ChanchalSakardeQH/WATERTANK-LEVEL-INDICATOR-with-Dashboard/water_level_indicator/dashboard_html.h

/*
  Water Tanks Monitor System - dashboard web page (HTML, CSS, JavaScript), served from flash
  woodyouloveit.com
  Copyright (C) 2026 Chanchal Sakarde. All Rights Reserved, except as granted by the license below.

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
  SPDX-License-Identifier: GPL-3.0-or-later
*/
// Dashboard web page, served from flash. Works offline (no external files).
#pragma once
#include <Arduino.h>

const char DASHBOARD_HTML[] PROGMEM = R"rawliteral(<!DOCTYPE html>
<html lang="en">
<!--
  Water Tanks Monitor System dashboard - woodyouloveit.com
  Copyright (C) 2026 Chanchal Sakarde. All Rights Reserved, except as granted by the GNU GPL v3 (or later).
  Source: https://github.com/ChanchalSakardeQH/WATERTANK-LEVEL-INDICATOR-with-Dashboard
-->
<head>
<meta charset="utf-8">
<meta name="viewport" content="width=device-width, initial-scale=1, viewport-fit=cover">
<meta name="theme-color" content="#0f766e">
<title>Water Tanks Monitor System | woodyouloveit.com</title>
<meta name="author" content="Chanchal Sakarde, woodyouloveit.com">
<link rel="icon" href="data:image/svg+xml,%3Csvg xmlns='http://www.w3.org/2000/svg' viewBox='0 0 32 32'%3E%3Cpath fill='%23e7004e' d='M16 29 3.5 16.5A7.5 7.5 0 0 1 16 6.2 7.5 7.5 0 0 1 28.5 16.5Z'/%3E%3C/svg%3E">
<style>
:root{--bg:#f1f5f9;--card:#fff;--text:#0f172a;--muted:#64748b;--line:#e2e8f0;--accent:#0f766e;--accent2:#14b8a6;
--danger:#dc2626;--warn:#d97706;--ok:#16a34a;--input:#f8fafc;--shadow:0 1px 3px rgba(15,23,42,.08),0 4px 16px rgba(15,23,42,.05)}
@media (prefers-color-scheme:dark){:root{--bg:#0b1220;--card:#131c2e;--text:#e2e8f0;--muted:#94a3b8;--line:#243047;
--input:#0f1726;--shadow:0 1px 3px rgba(0,0,0,.4)}}
*{box-sizing:border-box}
html,body{margin:0;background:var(--bg);color:var(--text);font-family:-apple-system,BlinkMacSystemFont,"Segoe UI",Roboto,Helvetica,Arial,sans-serif;-webkit-text-size-adjust:100%}
body{padding:env(safe-area-inset-top) env(safe-area-inset-right) env(safe-area-inset-bottom) env(safe-area-inset-left)}
/* brand */
.brandbar{display:flex;align-items:center;justify-content:space-between;gap:12px;background:#fff;padding:10px 20px;border-bottom:1px solid #e2e8f0}
.brandbar img{height:30px;width:auto;display:block}
.brandbar .site{color:#0f172a;font-weight:700;font-size:13px;text-decoration:none;white-space:nowrap}
.brandbar .site:hover{color:#e7004e}
@media (max-width:380px){.brandbar img{height:24px}.brandbar .site{font-size:12px}}
footer{line-height:1.8}footer a{color:inherit;font-weight:600}
.copy{font-weight:600;color:var(--text)}
.pdfrow{display:flex;flex-wrap:wrap;align-items:center;gap:10px 16px;margin-top:14px}
.pdfrow .btn{width:auto;padding:12px 20px}.pdfrow .help{margin:0;flex:1;min-width:200px}
header{display:flex;align-items:center;justify-content:space-between;gap:12px;padding:16px 20px;background:var(--accent);color:#fff}
header h1{font-size:18px;margin:0;font-weight:600;line-height:1.2}
header small{display:block;opacity:.8;font-weight:400;font-size:12px}
.chip{display:inline-flex;align-items:center;gap:6px;padding:5px 12px;border-radius:999px;font-size:13px;font-weight:600;background:rgba(255,255,255,.18);white-space:nowrap}
.chip i{width:8px;height:8px;border-radius:50%;background:#a7f3d0}
.chip.bad i{background:#fca5a5}.chip.warn i{background:#fcd34d}
main{max-width:1100px;margin:0 auto;padding:16px;display:grid;gap:16px;grid-template-columns:1fr}
@media (min-width:860px){main{padding:24px}#tabOverview{grid-template-columns:380px 1fr;grid-template-areas:'ban ban' 'level glance';align-items:start}
#tabAnalytics{grid-template-columns:1fr 1fr;grid-template-areas:'akpi akpi' 'achart achart' 'amotor ause' 'ahour anight' 'aset aset';align-items:start}
#aKpi{grid-area:akpi}#aChart{grid-area:achart}#aMotor{grid-area:amotor}#aUse{grid-area:ause}#aHour{grid-area:ahour}#aNight{grid-area:anight}#aSet{grid-area:aset}
#banners{grid-area:ban}
#tabOverview:has(#banners[hidden]){grid-template-areas:'level glance'}#cLevel{grid-area:level}#cGlance{grid-area:glance}
#tabSetup{grid-template-columns:1fr 1fr;grid-template-areas:'prof cal' 'site cal' 'site disp' 'power disp' 'rate dev' 'admin ota' 'wifi wifi';align-items:start}
#cProfile{grid-area:prof}#cPower{grid-area:power}#cAdmin{grid-area:admin}#cRate{grid-area:rate}#cOta{grid-area:ota}#cCal{grid-area:cal}#cSite{grid-area:site}#cDisp{grid-area:disp}#cWifi{grid-area:wifi}#cDev{grid-area:dev}}
.card{background:var(--card);border-radius:14px;box-shadow:var(--shadow);padding:18px}
.card h2{font-size:15px;margin:0 0 14px;color:var(--muted);font-weight:600;letter-spacing:.02em}
.hero{display:flex;gap:20px;align-items:stretch}
.tank{position:relative;width:110px;min-width:110px;height:230px;border:3px solid var(--line);border-top:none;border-radius:0 0 18px 18px;overflow:hidden;background:var(--input)}
.water{position:absolute;left:0;right:0;bottom:0;height:0;transition:height .8s ease,background-color .8s ease}
.water:before{content:"";position:absolute;left:0;right:0;top:-6px;height:12px;background:inherit;border-radius:50%;opacity:.7}
.leds{display:flex;flex-direction:column-reverse;gap:3px;height:230px;padding:2px 0}
.led{width:12px;flex:1 1 0;min-height:1px;max-height:6px;margin:auto 0;border-radius:2px;background:var(--line);transition:background-color .5s}
.big{font-size:56px;font-weight:700;line-height:1;margin:6px 0 4px}
.big small{font-size:22px;color:var(--muted);font-weight:600}
.kv{display:grid;grid-template-columns:auto 1fr;gap:6px 14px;font-size:14px;margin-top:14px}
.kv span{color:var(--muted)}.kv b{font-weight:600;text-align:right}
.alert{margin-top:12px;padding:10px 12px;border-radius:10px;font-size:13px;font-weight:600;display:none}
.alert.show{display:block}.alert.ok{background:rgba(22,163,74,.12);color:var(--ok)}.alert.info{background:rgba(15,118,110,.12);color:var(--accent)}
.alert a{color:inherit}.alert.bad{background:rgba(220,38,38,.12);color:var(--danger)}.alert.warn{background:rgba(217,119,6,.12);color:var(--warn)}
.live{display:flex;align-items:baseline;justify-content:space-between;padding:12px 14px;border-radius:10px;background:var(--input);margin-bottom:14px}
.live b{font-size:26px}
.row2{display:grid;grid-template-columns:1fr 1fr;gap:12px}
.row3{display:grid;grid-template-columns:1fr 1fr 1fr;gap:10px}.row3[hidden],.row2[hidden]{display:none}
.sel{width:100%;padding:11px 10px;font-size:16px;border:1px solid var(--line);border-radius:10px;background:var(--input);color:var(--text)}
h3.sub{font-size:14px;margin:20px 0 6px;color:var(--text)}
.slide{display:flex;align-items:center;gap:14px;margin:10px 0 6px}.slide input{flex:1;height:32px}.slide b{min-width:96px;text-align:right;font-size:18px}
.calprev{font-size:13px;line-height:1.5;padding:10px 12px;border-radius:10px;background:var(--input);margin:6px 0 10px}
.calprev.bad{background:rgba(220,38,38,.12);color:var(--danger)}.calprev.warn{background:rgba(217,119,6,.12);color:var(--warn)}
.ro{padding:11px 12px;border:1px dashed var(--line);border-radius:10px;font-size:16px}
.help a,.card p a{color:var(--accent);font-weight:600}
.hright{display:flex;align-items:center;gap:8px}
.adminBtn{border:1px solid rgba(255,255,255,.5);background:transparent;color:#fff;border-radius:999px;padding:5px 12px;font-size:13px;font-weight:600;cursor:pointer}
.adminBtn:hover{background:rgba(255,255,255,.15)}
.h2row{display:flex;align-items:center;justify-content:space-between;gap:8px}
.mini{font-size:12px;padding:4px 6px;border:1px solid var(--line);border-radius:8px;background:var(--input);color:var(--text)}
.viewer .adminOnlyNote{display:block}.adminOnlyNote{display:none}
.modal h2{margin-top:0}
.otaBar{height:10px;border-radius:999px;background:var(--input);border:1px solid var(--line);overflow:hidden;margin-top:12px}
.otaBar i{display:block;height:100%;width:0;background:var(--accent);transition:width .2s}
.litres{font-size:15px;color:var(--muted);margin:-2px 0 8px;font-weight:600}
.gstats{display:grid;grid-template-columns:repeat(3,1fr);gap:8px;margin-bottom:14px}.gstats .stat b{font-size:20px}
.seg[id=segUsage]{margin-bottom:0}
label{display:block;font-size:13px;color:var(--muted);margin-bottom:6px}
input[type=number],input[type=text],input[type=password]{width:100%;padding:11px 12px;font-size:16px;border:1px solid var(--line);border-radius:10px;background:var(--input);color:var(--text)}
input[type=range]{width:100%;accent-color:var(--accent)}
.field{margin-bottom:14px}
.btn{appearance:none;border:none;border-radius:10px;padding:12px 14px;min-height:44px;font-size:15px;font-weight:600;cursor:pointer;background:var(--accent);color:#fff;width:100%}
.btn:active{transform:scale(.98)}.btn:disabled{opacity:.5;cursor:not-allowed}
.btn.sec{background:var(--input);color:var(--text);border:1px solid var(--line)}
.btn.danger{background:transparent;color:var(--danger);border:1px solid var(--danger)}
.btns{display:grid;grid-template-columns:1fr 1fr;gap:10px;margin-bottom:12px}
.toggle{display:flex;align-items:center;justify-content:space-between;gap:12px;padding:10px 0;border-top:1px solid var(--line);font-size:14px}
.toggle:first-of-type{border-top:none}
.sw{position:relative;width:48px;height:28px;flex:none}.sw input{opacity:0;width:0;height:0}
.sw i{position:absolute;inset:0;border-radius:999px;background:var(--line);transition:.2s;cursor:pointer}
.sw i:after{content:"";position:absolute;left:3px;top:3px;width:22px;height:22px;border-radius:50%;background:#fff;transition:.2s;box-shadow:0 1px 2px rgba(0,0,0,.3)}
.sw input:checked+i{background:var(--accent)}.sw input:checked+i:after{transform:translateX(20px)}
.help{font-size:12px;color:var(--muted);margin:6px 0 0;line-height:1.5}
.toast{position:fixed;left:50%;bottom:calc(20px + env(safe-area-inset-bottom));transform:translateX(-50%) translateY(120px);background:#0f172a;color:#fff;padding:12px 18px;border-radius:12px;font-size:14px;transition:transform .25s,opacity .25s;z-index:9;opacity:0;visibility:hidden;max-width:90vw;text-align:center}
.toast.show{transform:translateX(-50%) translateY(0);opacity:1;visibility:visible}.toast.err{background:var(--danger)}
.rssi{display:inline-flex;gap:2px;align-items:flex-end;height:14px;vertical-align:middle;margin-left:6px}
.rssi i{width:4px;background:var(--line);border-radius:1px}.rssi i.on{background:var(--ok)}
.modal{position:fixed;inset:0;background:rgba(15,23,42,.55);display:none;align-items:center;justify-content:center;padding:20px;z-index:10}
.modal.show{display:flex}.modal .card{max-width:380px;width:100%}.modal p{margin:0 0 18px;line-height:1.5;font-size:15px}
@media (max-width:380px){.tank{width:84px;min-width:84px}.big{font-size:44px}.hero{gap:14px}}
.wgrid{display:grid;gap:18px}@media (min-width:860px){.wgrid{grid-template-columns:1fr 1fr;gap:32px}}
.scanhead{display:flex;align-items:center;justify-content:space-between;margin-bottom:8px}.scanhead label{margin:0}
.btn.small{width:auto;min-height:36px;padding:8px 16px;font-size:14px}
.netlist{border:1px solid var(--line);border-radius:10px;max-height:230px;overflow-y:auto;margin-bottom:14px;background:var(--input)}
.netlist .help{padding:12px;margin:0}
.net{display:flex;align-items:center;justify-content:space-between;width:100%;gap:10px;padding:12px 14px;border:none;border-top:1px solid var(--line);background:transparent;color:var(--text);font-size:15px;text-align:left;cursor:pointer;min-height:44px}
.net:first-child{border-top:none}.net:hover,.net.sel{background:rgba(20,184,166,.12)}
.net span{overflow:hidden;text-overflow:ellipsis;white-space:nowrap}.net small{color:var(--muted);flex:none;font-size:12px}
.pw{position:relative}.pw input{padding-right:70px}
.eye{position:absolute;right:6px;top:50%;transform:translateY(-50%);border:none;background:transparent;color:var(--accent);font-weight:600;font-size:13px;padding:8px;cursor:pointer}
.banner{background:var(--accent);color:#fff;border-radius:14px;padding:14px 18px;font-size:14px;line-height:1.5;display:none}
.banner.show{display:block}.banner a{color:#fff;font-weight:700}
.stats{display:flex;flex-wrap:wrap;gap:8px;margin-bottom:14px}
.stat{background:var(--input);border:1px solid var(--line);border-radius:10px;padding:8px 12px;font-size:13px;color:var(--muted)}
.stat b{display:block;font-size:18px;color:var(--text)}.stat.bad b{color:var(--danger)}.stat.warn b{color:var(--warn)}
.logbar{display:flex;flex-wrap:wrap;align-items:center;gap:10px;margin-bottom:10px}
.logbar select{padding:9px 10px;font-size:14px;border:1px solid var(--line);border-radius:10px;background:var(--input);color:var(--text)}
.chk{display:flex;align-items:center;gap:6px;font-size:14px;color:var(--text);margin:0}
.logbtns{display:flex;gap:8px;margin-left:auto}
.logbox{max-height:440px;overflow:auto;border:1px solid var(--line);border-radius:10px;background:var(--input);font:12.5px/1.45 ui-monospace,SFMono-Regular,Menlo,Consolas,monospace}
.logbox .help{padding:12px;margin:0;font-family:inherit}
.lr{display:grid;grid-template-columns:150px 56px 1fr;gap:10px;padding:7px 12px;border-top:1px solid var(--line)}
.lr:first-child{border-top:none}.lr time{color:var(--muted);white-space:nowrap}
.lr .tag{color:var(--muted);text-transform:uppercase;font-size:11px;padding-top:1px}
.lr.W .msg{color:var(--warn)}.lr.E .msg{color:var(--danger);font-weight:600}
.lr.boot{background:rgba(15,118,110,.10)}.lr.boot .msg{font-weight:600}
@media (max-width:600px){.lr{grid-template-columns:auto 1fr;gap:2px 10px}.lr .msg{grid-column:1/-1}.logbtns{margin-left:0}}
.tabs{display:flex;gap:4px;background:var(--accent);padding:0 12px;overflow-x:auto}
.tabs button{appearance:none;border:none;background:transparent;color:rgba(255,255,255,.75);font-size:15px;font-weight:600;padding:10px 14px 12px;cursor:pointer;border-bottom:3px solid transparent;white-space:nowrap}
.tabs button.on{color:#fff;border-bottom-color:#fff}
.tab[hidden]{display:none!important}#banners[hidden]{display:none!important}
.kpis{display:grid;grid-template-columns:repeat(auto-fill,minmax(150px,1fr));gap:10px}
.kpi{background:var(--input);border:1px solid var(--line);border-radius:12px;padding:12px}
.kpi span{display:block;font-size:12px;color:var(--muted);font-weight:600;letter-spacing:.02em}
.kpi b{display:block;font-size:20px;margin:4px 0 2px}.kpi small{font-size:12px;color:var(--muted)}
.kpi.bad b{color:var(--danger)}.kpi.warn b{color:var(--warn)}.kpi.ok b{color:var(--ok)}.kpi.live b{color:var(--accent)}
.chart{width:100%;min-height:60px;position:relative}
.chart svg{display:block;width:100%;height:auto;overflow:visible}
.chart .grid{stroke:var(--line);stroke-width:1}.chart .axis{fill:var(--muted);font-size:11px}
.chart .tip{position:absolute;top:0;pointer-events:none;background:var(--text);color:var(--card);font-size:12px;padding:4px 8px;border-radius:6px;white-space:nowrap;display:none;transform:translateX(-50%)}
.seg{display:inline-flex;border:1px solid var(--line);border-radius:10px;overflow:hidden;margin-bottom:10px}
.seg button{border:none;background:var(--input);color:var(--text);padding:8px 14px;font-size:14px;cursor:pointer}
.seg button.on{background:var(--accent);color:#fff}
.legend{display:flex;flex-wrap:wrap;gap:14px;font-size:12px;color:var(--muted);margin-top:6px}
.legend i{display:inline-block;width:12px;height:12px;border-radius:3px;vertical-align:-2px;margin-right:5px}
table.nt{width:100%;border-collapse:collapse;font-size:14px}
.nt th{text-align:left;color:var(--muted);font-weight:600;font-size:12px;padding:6px 4px;border-bottom:1px solid var(--line)}
.nt td{padding:8px 4px;border-bottom:1px solid var(--line)}.nt td:last-child{text-align:right}
.pill{display:inline-block;padding:2px 10px;border-radius:999px;font-size:12px;font-weight:700}
.pill.ok{background:rgba(22,163,74,.14);color:var(--ok)}.pill.warn{background:rgba(217,119,6,.14);color:var(--warn)}
.pill.bad{background:rgba(220,38,38,.14);color:var(--danger)}.pill.na{background:var(--input);color:var(--muted)}
.fl{font-size:13px;margin-top:12px;border-top:1px solid var(--line)}.fl div{padding:7px 0;border-bottom:1px solid var(--line);display:flex;justify-content:space-between;gap:10px}
.fl div span:last-child{color:var(--muted);text-align:right}
select.inp{width:100%;padding:11px 12px;font-size:16px;border:1px solid var(--line);border-radius:10px;background:var(--input);color:var(--text)}
footer{text-align:center;color:var(--muted);font-size:12px;padding:8px 0 24px}
</style>
</head>
<body>
<div class="brandbar">
  <a href="https://woodyouloveit.com" target="_blank" rel="noopener"><img id="brandLogo" alt="woodyouloveit.com" src="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"></a>
  <a class="site" href="https://woodyouloveit.com" target="_blank" rel="noopener">woodyouloveit.com</a>
</div>
<header>
  <h1><span id="hTitle">Water Tanks Monitor System</span><small id="hSub">woodyouloveit.com</small></h1>
  <div class="hright"><div class="chip" id="chip"><i></i><span id="chipText">Connecting…</span></div>
    <button class="adminBtn" id="btnAdmin" onclick="adminClick()">Admin</button></div>
</header>
<nav class="tabs" id="tabs">
  <button data-tab="overview" class="on">Overview</button>
  <button data-tab="analytics">Analytics</button>
  <button data-tab="setup">Setup</button>
  <button data-tab="log">Log</button>
</nav>

<main id="tabOverview" class="tab">
  <div id="banners" style="display:grid;gap:12px">
  <div class="banner" id="siteBanner">Name this tank: add the society or organisation, building and tank in <a href="#cSite">Setup → Site details</a>. The names appear on the dashboard and in reports.</div>
  <div class="banner" id="setupBanner">Not connected to your home Wi-Fi yet. <a href="#cWifi">Set up Wi-Fi</a> in Setup to use the dashboard from your home network.</div>
  </div>

  <section class="card" id="cLevel">
    <h2 class="h2row"><span>WATER LEVEL</span>
      <select id="unitSel" class="mini" title="Units on this device (browser)"><option value="">Units: default</option>
        <option value="0">cm</option><option value="1">mm</option><option value="2">inch</option></select></h2>
    <div class="hero">
      <div class="tank"><div class="water" id="water"></div></div>
      <div class="leds" id="leds" title="LED strip preview"></div>
      <div style="flex:1;min-width:0">
        <div class="big"><span id="pct">--</span><small>%</small></div>
        <div class="litres" id="litres"></div>
        <div class="kv">
          <span>Distance</span><b id="dist">-- cm</b>
          <span>Empty at</span><b id="kvEmpty">-- cm</b>
          <span>Full at</span><b id="kvFull">-- cm</b>
        </div>
      </div>
    </div>
    <div class="alert bad" id="alertFault">Sensor fault: no echo. Check the sensor wiring and that the probe faces the water.</div>
    <div class="alert warn" id="alertLow">Low water level.</div>
    <div class="alert info" id="alertFill"></div>
    <div class="alert bad" id="alertLeak"></div>
  </section>

  <section class="card" id="cGlance">
    <h2>TANK AT A GLANCE</h2>
    <div class="gstats">
      <div class="stat"><b id="gWater">--</b>water now</div>
      <div class="stat"><b id="gFree">--</b>space left</div>
      <div class="stat"><b id="gCap">--</b>capacity</div>
    </div>
    <div class="kv" style="margin-top:0">
      <span>Site</span><b id="gSite">--</b>
      <span>Usage</span><b id="gUsage">--</b>
      <span>Tank</span><b id="gTank">--</b>
      <span>Water depth when full</span><b id="gDepth">--</b>
      <span>Calibrated range</span><b id="gRange">--</b>
      <span>Sensor to full water line</span><b id="gGap">--</b>
      <span id="gResL">1 cm of water</span><b id="gRes">--</b>
    </div>
    <div class="alert warn" id="gWarn"></div>
    <p class="help adminLink" style="margin-top:12px"><a href="#setup">Change tank, usage and calibration in Setup</a></p>
  </section>
</main>

<main id="tabSetup" class="tab" hidden>
  <section class="card" id="cProfile">
    <h2>USAGE &amp; TANK</h2>
    <div class="field"><label>Usage</label>
      <div class="seg" id="segUsage"><button data-v="0" class="on">Domestic</button><button data-v="1">Commercial</button></div></div>
    <div class="row2">
      <div class="field"><label for="inLoc">Tank location</label><select id="inLoc" class="sel">
        <option value="0">Overhead (roof)</option><option value="1">Loft / bathroom</option>
        <option value="2">Underground sump</option><option value="3">Other</option></select></div>
      <div class="field"><label for="inShape">Tank shape</label><select id="inShape" class="sel">
        <option value="0">Rectangular (box, loft)</option><option value="1">Vertical cylinder</option></select></div>
    </div>
    <div class="field"><label for="inPreset">Tank size</label><select id="inPreset" class="sel"></select></div>
    <div class="row3" id="dimRect">
      <div class="field"><label for="inLen">Length (<span class="uL">mm</span>)</label><input type="number" id="inLen" min="0" max="20000" inputmode="numeric"></div>
      <div class="field"><label for="inWid">Width (<span class="uL">mm</span>)</label><input type="number" id="inWid" min="0" max="20000" inputmode="numeric"></div>
      <div class="field"><label for="inHgt">Height (<span class="uL">mm</span>)</label><input type="number" id="inHgt" min="0" max="20000" inputmode="numeric"></div>
    </div>
    <div class="row2" id="dimCyl" hidden>
      <div class="field"><label for="inDia">Diameter (<span class="uL">mm</span>)</label><input type="number" id="inDia" min="0" max="20000" inputmode="numeric"></div>
      <div class="field"><label for="inHgtC">Height (<span class="uL">mm</span>)</label><input type="number" id="inHgtC" min="0" max="20000" inputmode="numeric"></div>
    </div>
    <div class="row2">
      <div class="field"><label for="inDepth">Water depth when full (<span class="uL">mm</span>)</label><input type="number" id="inDepth" min="0" max="20000" inputmode="numeric">
        <p class="help">Tank bottom to the overflow pipe: the highest the water gets.</p></div>
      <div class="field"><label for="inCapP">Capacity (litres)</label><input type="number" id="inCapP" min="0" max="1000000" inputmode="numeric">
        <p class="help" id="capHint"></p></div>
    </div>
    <div class="alert info" id="profTip"></div>
    <div class="btns" style="margin-top:14px">
      <button class="btn" onclick="saveProfile()">Save tank</button>
      <button class="btn sec" onclick="applyRecommended()">Recommended settings</button>
    </div>
    <p class="help" id="recHelp"></p>
  </section>

  <section class="card" id="cCal">
    <h2>CALIBRATION</h2>
    <div class="live"><span>Live sensor reading <small class="help" id="liveMode"></small></span><b id="liveDist">-- cm</b></div>

    <h3 class="sub">1 · How full is the tank right now?</h3>
    <p class="help">Slide to the current water level. With the water depth from <a href="#cProfile">Usage &amp; tank</a>,
      the empty and full points are worked out from the live reading. No need to empty or fill the tank.</p>
    <div class="slide"><input type="range" id="inNow" min="0" max="100" step="1" value="50"><b id="nowVal">50%</b></div>
    <div class="calprev" id="prevSlider"></div>
    <button class="btn" id="btnSlider" onclick="calSlider()">Save calibration from current level</button>

    <h3 class="sub">2 · From measurements</h3>
    <div class="row2">
      <div class="field"><label for="inGap">Sensor face to full water line (<span class="uL">cm</span>)</label><input type="number" id="inGap" step="0.5" min="15" max="400" inputmode="decimal"></div>
      <div class="field"><label>Water depth when full</label><div class="ro" id="depthShow">--</div></div>
    </div>
    <div class="calprev" id="prevMeas"></div>
    <button class="btn sec" id="btnMeas" onclick="calMeasured()">Save calibration from measurements</button>

    <h3 class="sub">3 · Tank is empty or full right now</h3>
    <div class="btns">
      <button class="btn sec" id="btnEmpty" onclick="calNow('empty')">Tank is EMPTY now</button>
      <button class="btn sec" id="btnFull" onclick="calNow('full')">Tank is FULL now</button>
    </div>
    <div class="row2" style="margin-top:4px">
      <div class="field"><label for="inEmpty">Empty distance (<span class="uL">cm</span>)</label><input type="number" id="inEmpty" step="0.5" min="20" max="450" inputmode="decimal"></div>
      <div class="field"><label for="inFull">Full distance (<span class="uL">cm</span>)</label><input type="number" id="inFull" step="0.5" min="15" max="440" inputmode="decimal"></div>
    </div>
    <button class="btn sec" onclick="calManual()">Save distances</button>
    <p class="help">Now: empty at <b id="calNowE">--</b>, full at <b id="calNowF">--</b> from the sensor.
      The sensor can't measure closer than about 20–25 cm, so the full water line must be at least that far below it.</p>
  </section>

  <section class="card" id="cSite">
    <h2>SITE DETAILS</h2>
    <div class="field"><label for="inOrg">Society / organisation</label><input type="text" id="inOrg" maxlength="48" placeholder="e.g. NYATI" autocomplete="organization"></div>
    <div class="row2">
      <div class="field"><label for="inBld">Building</label><input type="text" id="inBld" maxlength="32" placeholder="e.g. Tower A"></div>
      <div class="field"><label for="inTank">Tank</label><input type="text" id="inTank" maxlength="32" placeholder="e.g. Overhead Tank 1"></div>
    </div>
    <div class="kv" style="margin-top:0">
      <span>Hotspot name</span><b id="sAp">--</b>
      <span>Web address</span><b id="sHost">--</b>
    </div>
    <div class="alert info" id="sRestart"></div>
    <div class="btns" style="margin-top:14px">
      <button class="btn" onclick="saveSite()">Save site details</button>
      <button class="btn sec" id="btnSiteRestart" onclick="restartDev()">Restart device</button>
    </div>
    <p class="help">Used on this dashboard, in PDF reports and downloaded logs. The hotspot name and web address are made from the building and tank
      names, so every tank in the society gets its own. They change after a restart.</p>
  </section>

  <section class="card" id="cDisp">
    <h2>DISPLAY &amp; SENSOR SETTINGS</h2>
    <div class="field"><label>Units for everyone (default)</label>
      <div class="seg" id="segUnits" style="margin-bottom:4px"><button data-v="1">mm</button><button data-v="0">cm</button><button data-v="2">inch</button></div>
      <p class="help">Used on the dashboard and in PDF reports. Each viewer can still pick other units in the Water level card.</p></div>
    <div class="field"><label for="inLeds">Number of LEDs on the strip</label><input type="number" id="inLeds" min="1" max="300" step="1" inputmode="numeric">
      <p class="help" id="ampHelp"></p></div>
    <div class="field"><label>LED brightness: <b id="brVal">--</b></label><input type="range" id="inBr" min="5" max="255" step="5"></div>
    <div class="field"><label>Low water alarm below: <b id="lowVal">--</b>%</label><input type="range" id="inLow" min="0" max="50" step="1"></div>
    <div class="toggle"><span>Strip mounted top-down (LED 1 at top)</span><label class="sw"><input type="checkbox" id="inRev"><i></i></label></div>
    <div class="toggle"><span>Whole bar one color (by level)</span><label class="sw"><input type="checkbox" id="inCbl"><i></i></label></div>
    <div class="field" style="margin-top:10px"><label for="inTrig">Sensor trigger pulse (µs)</label><input type="number" id="inTrig" min="10" max="1000" step="10" inputmode="numeric">
      <p class="help">The AJ-SR04M needs 50–500 µs. Default 100.</p></div>
    <div class="btns">
      <button class="btn" onclick="saveSettings()">Save settings</button>
      <button class="btn sec" onclick="resetDefaults()">Defaults</button>
    </div>
  </section>

  <section class="card" id="cPower">
    <h2>POWER &amp; RADIO</h2>
    <div class="toggle" style="border-top:none"><span>Power saving (production mode)<br><span class="help">CPU at 80 MHz (ESP32), LED strip refreshed only when it changes,
      Wi-Fi power saving while the hotspot is off. Recommended for installed devices. How often the sensor is read is set in Update rate.</span></span>
      <label class="sw"><input type="checkbox" id="inEco"><i></i></label></div>
    <div class="field" style="margin-top:10px"><label for="inApMode">Hotspot</label>
      <select id="inApMode" class="sel"><option value="0">Automatic: on when home Wi-Fi is unavailable</option>
        <option value="2">On demand: press BOOT to turn on, off after 10 min idle</option><option value="1">Always on</option></select>
      <p class="help" id="apModeHelp"></p></div>
    <div class="field"><label>Wi-Fi transmit power</label>
      <div class="seg" id="segTx" style="margin-bottom:4px"><button data-v="2">Low</button><button data-v="0">Medium</button><button data-v="1">High</button></div>
      <p class="help">Lower power means less heat and less interference. Use High only if the signal to the router or phone is weak.</p></div>
    <div class="kv" style="margin-top:0">
      <span>Mode now</span><b id="pMode">--</b>
      <span>CPU</span><b id="pCpu">--</b>
      <span>Transmit power</span><b id="pTx">--</b>
      <span>Update rate</span><b id="pRate">--</b>
    </div>
    <div style="margin-top:14px"><button class="btn" onclick="savePower()">Save power settings</button></div>
  </section>

  <section class="card" id="cRate">
    <h2>UPDATE RATE</h2>
    <p class="help" style="margin-top:0">How often the water level is measured, and how often an open dashboard refreshes. Slower means less
      sensor and radio activity, lower power and a cooler board. A tank level changes slowly, so Eco is plenty for daily use.</p>
    <div class="field" style="margin-top:10px"><label for="inRate">Profile</label>
      <select id="inRate" class="sel">
        <option value="0">Eco: sensor every 5 s, dashboard every 10 s (recommended)</option>
        <option value="1">Balanced: sensor every 2 s, dashboard every 5 s</option>
        <option value="2">Responsive: sensor every 0.5 s, dashboard every 2 s</option>
        <option value="3">Custom</option></select></div>
    <div class="row2" id="rateCustom" hidden>
      <div class="field"><label for="inSensS">Sensor reading every (seconds)</label><input type="number" id="inSensS" min="0.2" max="30" step="0.1" inputmode="decimal"></div>
      <div class="field"><label for="inRefS">Dashboard refresh every (seconds)</label><input type="number" id="inRefS" min="2" max="60" step="1" inputmode="numeric"></div>
    </div>
    <div class="kv" style="margin-top:0">
      <span>Sensor readings</span><b id="rPerH">--</b>
      <span>Level follows a change within</span><b id="rReact">--</b>
      <span>"No echo" shown after</span><b id="rFault">--</b>
      <span>Open dashboard refreshes</span><b id="rRefresh">--</b>
    </div>
    <p class="help">Not affected: history (every 2 min), fill detection (every 10 s) and the night leak check.
      While an admin has this Setup tab open, the device reads every 0.5 s so calibration stays live, then returns to this rate.</p>
    <div style="margin-top:12px"><button class="btn" onclick="saveRate()">Save update rate</button></div>
  </section>

  <section class="card" id="cOta">
    <h2>FIRMWARE UPDATE</h2>
    <div class="kv" style="margin-top:0">
      <span>Installed</span><b id="otaCur">--</b>
      <span>Board</span><b id="otaBoard">--</b>
      <span>Space for an update</span><b id="otaMax">--</b>
    </div>
    <p class="help">In Arduino IDE use <b>Sketch → Export Compiled Binary</b>, then pick <b>water_level_indicator.ino.bin</b> from the sketch's
      <b>build</b> folder (not the .bootloader, .partitions or .merged file). Settings, Wi-Fi, calibration, history and logs are kept.</p>
    <input type="file" id="fileOta" accept=".bin,application/octet-stream" hidden onchange="otaPick(this)">
    <div style="margin-top:12px"><button class="btn" id="btnOta" onclick="$('fileOta').click()">Choose firmware file…</button></div>
    <div class="otaBar" id="otaBar" hidden><i id="otaFill"></i></div>
    <p class="help" id="otaMsg"></p>
  </section>

  <section class="card" id="cAdmin">
    <h2>ADMIN &amp; BACKUP</h2>
    <p class="help" style="margin-top:0">Without logging in, people see the Overview and Analytics tabs only. They can't change settings,
      clear history, or restart the device.</p>
    <div class="btns" style="margin-top:12px">
      <button class="btn sec" onclick="openPwModal(false)">Change password</button>
      <button class="btn sec" onclick="adminLogout()">Log out</button>
    </div>
    <h3 class="sub">Settings backup</h3>
    <p class="help">Saves site, tank, calibration, units, alarms, analytics, display and power settings to a file, to restore later or
      on another device, and to attach to reports. Wi-Fi passwords and the admin password are never included.</p>
    <div class="kv" style="margin:8px 0 0"><span>Settings ID now</span><b id="setId">--</b></div>
    <div class="btns" style="margin-top:12px">
      <button class="btn" onclick="exportSettings()">Export settings</button>
      <button class="btn sec" onclick="$('fileImport').click()">Import settings</button>
    </div>
    <input type="file" id="fileImport" accept=".json,application/json" hidden onchange="importSettings(this)">
    <p class="help">The Settings ID also appears in PDF reports, so a report can be matched to the exported settings file.</p>
  </section>

  <section class="card" id="cWifi">
    <h2>WI-FI SETTINGS</h2>
    <div class="wgrid">
      <div>
        <div class="kv" style="margin-top:0">
          <span>Home network</span><b id="wSaved">--</b>
          <span>Status</span><b id="wState">--</b>
          <span>Signal</span><b><span id="rssiTxt">--</span><span class="rssi" id="rssiBars"><i style="height:4px"></i><i style="height:7px"></i><i style="height:10px"></i><i style="height:14px"></i></span></b>
          <span>Home address</span><b id="wIp">--</b>
          <span>Hotspot</span><b id="wAp">--</b>
        </div>
        <div class="alert" id="wMsg"></div>
        <p class="help" style="margin-top:12px">The hotspot <b class="apName">--</b> lets you reach this page at <b>http://192.168.4.1</b> when the device isn't on your home Wi-Fi.
          If it's off, press the <b>BOOT</b> button on the board to turn it on.</p>
        <p class="help">Hotspot mode: <b id="wApMode">--</b>. <a href="#cPower">Change in Power &amp; radio</a>.</p>
      </div>
      <div>
        <div class="scanhead"><label>Available networks</label><button class="btn sec small" id="btnScan" onclick="scan()">Scan</button></div>
        <div class="netlist" id="netList"><p class="help">Press Scan to find networks.</p></div>
        <div class="field"><label for="inSsid">Network name (SSID)</label><input type="text" id="inSsid" maxlength="32" autocomplete="off" autocapitalize="none" autocorrect="off" spellcheck="false"></div>
        <div class="field"><label for="inPass">Password</label><div class="pw"><input type="password" id="inPass" maxlength="63" autocomplete="off" autocapitalize="none" autocorrect="off" spellcheck="false"><button type="button" class="eye" id="btnEye" onclick="togglePw()">Show</button></div></div>
        <div class="btns">
          <button class="btn" onclick="connectWifi()">Connect</button>
          <button class="btn danger" onclick="forgetWifi()">Forget Wi-Fi</button>
        </div>
        <p class="help">Leave the password empty for open networks.</p>
      </div>
    </div>
  </section>

  <section class="card" id="cDev">
    <h2>DEVICE</h2>
    <div class="kv" style="margin-top:0">
      <span>Board</span><b id="board">--</b>
      <span>Firmware</span><b id="fw">--</b>
      <span>Uptime</span><b id="uptime">--</b>
      <span>Last restart</span><b id="reset">--</b>
      <span>Boot count</span><b id="boot">--</b>
      <span>Free memory</span><b id="heap">--</b>
      <span id="vccL">Supply voltage</span><b id="vcc">--</b>
      <span>Log storage</span><b id="logStore">--</b>
    </div>
    <div style="margin-top:16px"><button class="btn sec" onclick="restartDev()">Restart device</button></div>
  </section>
</main>

<main id="tabAnalytics" class="tab" hidden>
  <section class="card" id="aKpi">
    <h2>TANK ANALYTICS</h2>
    <div class="alert info" id="aMsg"></div>
    <div class="kpis" id="kpis"></div>
    <div class="pdfrow">
      <button class="btn" id="btnPdf" onclick="exportPdf()">Download PDF report</button>
      <p class="help">Last 7 days with charts, fills and night checks, branded with the woodyouloveit.com logo.
        On the hotspot's pop-up page, open the dashboard in your normal browser first so the download is allowed.</p>
    </div>
  </section>
  <section class="card" id="aChart">
    <h2>LEVEL HISTORY</h2>
    <div class="seg" id="rangeSeg"><button data-h="24" class="on">24 h</button><button data-h="72">3 days</button><button data-h="168">7 days</button><button data-h="336">14 days</button></div>
    <div class="chart" id="levelChart"></div>
    <div class="legend"><span><i style="background:rgba(22,163,74,.22)"></i>Filling (motor on)</span><span><i style="background:rgba(100,116,139,.16)"></i>Night check window</span></div>
  </section>
  <section class="card" id="aMotor">
    <h2>MOTOR RUN TIME PER DAY</h2>
    <div class="chart" id="motorChart"></div>
    <div class="fl" id="fillList"></div>
  </section>
  <section class="card" id="aUse">
    <h2>WATER USED PER DAY</h2>
    <div class="chart" id="useChart"></div>
    <p class="help">Counted from level drops outside fills. Small changes below the sensor noise are ignored.</p>
  </section>
  <section class="card" id="aHour">
    <h2>USAGE BY HOUR OF DAY</h2>
    <div class="chart" id="hourChart"></div>
    <p class="help" id="hourHelp">Average per day. The busiest hours are highlighted.</p>
  </section>
  <section class="card" id="aNight">
    <h2>NIGHT LEAK CHECK</h2>
    <div id="nightTable"></div>
    <p class="help" id="nightHelp"></p>
  </section>
  <section class="card adminOnly" id="aSet">
    <h2>ANALYTICS SETTINGS</h2>
    <div class="alert info adminOnlyNote" id="aSetNote" style="margin:0 0 14px">View only. <a href="#" onclick="openLogin();return false">Log in as admin</a> to change analytics settings or clear the history.</div>
    <div class="row2">
      <div class="field"><label for="inCap">Tank capacity (litres)</label><input type="number" id="inCap" min="0" max="1000000" step="50" inputmode="numeric" placeholder="e.g. 1000">
        <p class="help">Optional. Shows amounts in litres (assumes straight tank walls). 0 = show %.</p></div>
      <div class="field"><label for="inFillCm">Fill detection: minimum rise (<span class="uL">cm</span>/min)</label><input type="number" id="inFillCm" min="0.1" max="20" step="0.1" inputmode="decimal">
        <p class="help">Lower it if slow fills are missed, raise it if you see false fills. Default 0.5 cm/min.</p></div>
    </div>
    <div class="row2">
      <div class="field"><label for="inNs">Night check from</label><select class="inp" id="inNs"></select></div>
      <div class="field"><label for="inNe">to</label><select class="inp" id="inNe"></select></div>
    </div>
    <div class="field"><label for="inLeak">Possible leak if the level drops more than (<span class="uL">cm</span>) during the night window</label><input type="number" id="inLeak" min="0.2" max="50" step="0.1" inputmode="decimal">
      <p class="help">Pick a quiet time when nobody uses water. Default 01:00–05:00 and 1.5 cm.</p></div>
    <div class="btns">
      <button class="btn" onclick="saveAnalytics()">Save analytics settings</button>
      <button class="btn danger" onclick="clearHistory()">Clear history</button>
    </div>
  </section>
</main>

<main id="tabLog" class="tab" hidden>
  <section class="card" id="cLog">
    <h2>CONNECTIVITY LOG</h2>
    <div class="stats" id="logStats"></div>
    <div class="logbar">
      <select id="logFilter" onchange="renderLog()">
        <option value="all">All events</option><option value="net">Wi-Fi &amp; hotspot</option>
        <option value="warn">Warnings &amp; errors</option><option value="boot">Restarts</option>
      </select>
      <label class="chk"><input type="checkbox" id="logAuto" checked> Auto-refresh</label>
      <div class="logbtns">
        <button class="btn sec small" onclick="loadLog()">Refresh</button>
        <button class="btn sec small" onclick="downloadLog()">Download</button>
        <button class="btn danger small" onclick="clearLog()">Clear</button>
      </div>
    </div>
    <div class="logbox" id="logBox"><p class="help">Loading…</p></div>
    <p class="help">Newest first. Saved in flash, so it survives restarts and power cuts (about 300–400 events).
      Events from before the clock was known show as boot number + time since that start.</p>
  </section>
</main>
<footer>
  <div><span id="fSite">Water Tanks Monitor System</span> · <span id="host"></span></div>
  <div class="copy">© 2026 Chanchal Sakarde. All Rights Reserved. · <a href="https://woodyouloveit.com" target="_blank" rel="noopener">woodyouloveit.com</a></div>
  <div>Open source under the <a href="https://www.gnu.org/licenses/gpl-3.0.html" target="_blank" rel="noopener">GNU GPL v3</a> ·
    <a href="https://github.com/ChanchalSakardeQH/WATERTANK-LEVEL-INDICATOR-with-Dashboard" target="_blank" rel="noopener">Source code</a></div>
</footer>
<div class="toast" id="toast"></div>
<div class="modal" id="loginModal"><div class="card"><h2>ADMIN LOGIN</h2>
  <div class="field"><label for="inPw">Password</label><input type="password" id="inPw" autocomplete="current-password"></div>
  <p class="help" id="loginErr" style="color:var(--danger)"></p>
  <div class="btns" style="margin:0"><button class="btn sec" onclick="closeLogin()">Cancel</button><button class="btn" id="btnLogin" onclick="doLogin()">Log in</button></div>
  <p class="help" style="margin-top:12px">Forgot it? Hold the <b>BOOT</b> button on the board for 10 seconds (the strip flashes red) to reset the password to <b>admin</b>.</p>
</div></div>
<div class="modal" id="pwModal"><div class="card"><h2>CHANGE ADMIN PASSWORD</h2>
  <p class="help" id="pwNote"></p>
  <div class="field"><label for="inPw1">New password</label><input type="password" id="inPw1" autocomplete="new-password"></div>
  <div class="field"><label for="inPw2">Repeat new password</label><input type="password" id="inPw2" autocomplete="new-password"></div>
  <p class="help" id="pwErr" style="color:var(--danger)"></p>
  <div class="btns" style="margin:0"><button class="btn sec" id="btnPwCancel" onclick="closePwModal()">Cancel</button><button class="btn" onclick="savePw()">Save password</button></div>
</div></div>
<div class="modal" id="modal"><div class="card"><p id="modalMsg"></p>
  <div class="btns" style="margin:0"><button class="btn sec" id="modalNo">Cancel</button><button class="btn" id="modalYes">OK</button></div></div></div>

<script>
const $=id=>document.getElementById(id);
const sleep=ms=>new Promise(r=>setTimeout(r,ms));
let N=0,st=null,formLoaded=false,online=false,timeSent=false,logRows=[];
function buildLeds(n){if(n===N)return;N=n;const box=$('leds');box.innerHTML='';
  box.style.gap=(n<=40?3:n<=80?2:n<=120?1:0)+'px';
  for(let i=0;i<n;i++){const d=document.createElement('div');d.className='led';box.appendChild(d);}}
const posT=i=>N>1?i/(N-1):1;

function ledColor(t){t=Math.min(1,Math.max(0,t));let r,g;
  if(t<.5){r=255;g=Math.round(t*510);}else{r=Math.round((1-t)*510);g=255;}return `rgb(${r},${g},0)`;}
function toast(msg,err){const t=$('toast');t.textContent=msg;t.className='toast show'+(err?' err':'');
  clearTimeout(t._h);t._h=setTimeout(()=>t.className='toast'+(err?' err':''),3500);}
function ask(msg){return new Promise(res=>{$('modalMsg').textContent=msg;$('modal').classList.add('show');
  const done=v=>{$('modal').classList.remove('show');res(v);};$('modalYes').onclick=()=>done(true);$('modalNo').onclick=()=>done(false);});}
function fmtUp(s){const d=Math.floor(s/86400),h=Math.floor(s%86400/3600),m=Math.floor(s%3600/60);
  return (d?d+'d ':'')+(d||h?h+'h ':'')+m+'m';}
function bars(rssi){return rssi>-55?4:rssi>-65?3:rssi>-75?2:1;}
function setAlert(el,cls,html){el.className='alert'+(cls?' show '+cls:'');if(cls)el.innerHTML=html;}
function esc(s){const d=document.createElement('div');d.textContent=s;return d.innerHTML;}

function render(){
  const s=st,w=s.wifi,lvl=s.valid?s.level:0;
  $('pct').textContent=s.valid?Math.round(s.level):'--';
  $('dist').textContent=s.valid?fmtL(s.distance):'no echo';
  $('liveDist').textContent=s.valid?fmtL(s.distance):'no echo';
  if($('liveMode'))$('liveMode').textContent=s.rate&&s.rate.live?'· live, every 0.5 s':'';
  $('kvEmpty').textContent=fmtL(s.empty);$('kvFull').textContent=fmtL(s.full);
  const wt=$('water');wt.style.height=(s.valid?lvl:0)+'%';wt.style.backgroundColor=ledColor(lvl/100);
  buildLeds(s.leds);
  const lit=lvl/100*N,leds=$('leds').children;
  for(let i=0;i<N;i++){const on=s.valid&&i<Math.round(lit);
    leds[i].style.backgroundColor=on?ledColor(s.colorByLevel?lvl/100:posT(i)):'';}
  const low=s.valid&&lvl<s.lowAlarm;
  $('alertFault').classList.toggle('show',!s.valid);$('alertLow').classList.toggle('show',low);
  $('chip').className='chip'+(!s.valid?' bad':low?' warn':'');
  $('chipText').textContent=!s.valid?'Sensor fault':low?'Low water':'Online';
  $('btnEmpty').disabled=$('btnFull').disabled=!s.valid;

  // Wi-Fi
  const conn=w.state==='connected';
  $('setupBanner').classList.toggle('show',!w.saved&&w.state!=='connecting'&&!conn);
  renderSite();if(!siteLoaded)fillSite();
  applyUnitLabels();applyRole();
  renderGlance();renderPower();if(!profLoaded)fillProfile();else if(tab==='setup')calPreview();
  if(isAdmin()){$('setId').textContent=settingsId();renderOta();fillRate();}
  $('banners').hidden=!isAdmin()||!document.querySelector('#banners .banner.show');   // setup banners are for admins
  $('wSaved').textContent=w.saved||'Not set';
  $('wState').textContent={connected:'Connected',connecting:'Connecting…',failed:'Not reachable',none:'Not set up'}[w.state];
  $('rssiTxt').textContent=conn?w.rssi+' dBm':'--';
  [...$('rssiBars').children].forEach((b,i)=>b.classList.toggle('on',conn&&i<bars(w.rssi)));
  $('wIp').textContent=conn?w.ip:'--';
  $('wAp').textContent=w.ap?`On · ${w.apClients} device${w.apClients==1?'':'s'}`:'Off';
  const m=$('wMsg');
  if(w.state==='connecting')setAlert(m,'info',esc(w.msg));
  else if(conn&&w.ap&&w.apOffIn>0)setAlert(m,'ok',`Connected to <b>${esc(w.ssid)}</b>. Switch your phone or PC back to your home Wi-Fi and open
    <a href="http://${w.host}.local">http://${w.host}.local</a> or <a href="http://${w.ip}">http://${w.ip}</a>.
    The hotspot turns off in ${w.apOffIn} s.`);
  else if(w.state==='failed')setAlert(m,'bad',esc(w.msg));
  else if(w.state==='none')setAlert(m,'info',esc(w.msg));
  else setAlert(m,'','');

  $('board').textContent=s.board;$('fw').textContent=s.fw;$('uptime').textContent=fmtUp(s.uptime);$('reset').textContent=s.reset;
  $('boot').textContent='#'+s.boot;$('heap').textContent=(s.heap/1024).toFixed(1)+' KB (lowest '+(s.minHeap/1024).toFixed(1)+' KB)';
  $('vcc').textContent=s.vcc?(s.vcc/1000).toFixed(2)+' V':'';$('vcc').style.display=$('vccL').style.display=s.vcc?'':'none';
  $('logStore').textContent=s.logStore==='flash'?'Flash (kept after restart)':'Memory only (lost on restart)';
  $('host').textContent=conn?`${w.host}.local · ${w.ip}`:`hotspot · ${w.apIp}`;
  const fa=$('alertFill');
  if(s.filling)setAlert(fa,'info',`Filling (motor on) · rising ${fmtRate(s.fillRate)}`+(s.fillEta>=0?` · full in about ${dur(s.fillEta)}`:''));
  else setAlert(fa,'','');
  if(!formLoaded)fillForm();
}

// ---- Usage & tank profile ----
// Loft tank sizes (rated litres; outer length x width x height in mm)
const PRESETS=[null,
  {cap:150,l:710,w:710,h:400},{cap:225,l:1035,w:725,h:385},{cap:270,l:1100,w:735,h:425},
  {cap:400,l:1120,w:875,h:420},{cap:500,l:1450,w:915,h:445},{cap:1000,l:1650,w:1080,h:685}];
const USAGE=['Domestic','Commercial'],LOCS=['Overhead (roof)','Loft / bathroom','Underground sump','Other'];
let usageSel=0,profLoaded=false;
const iv=id=>{const v=parseFloat($(id).value);return isFinite(v)?v:0;};
function presetLabel(i){const p=PRESETS[i];return `Loft tank ${p.cap} L · ${p.l} × ${p.w} × ${p.h} mm`;}
function buildPresets(){const sel=$('inPreset'),shape=+$('inShape').value,cur=sel.value;
  sel.innerHTML='<option value="0">Custom size</option>'+(shape===0?PRESETS.slice(1).map((p,i)=>`<option value="${i+1}">${presetLabel(i+1)}</option>`).join(''):'');
  sel.value=[...sel.options].some(o=>o.value===cur)?cur:'0';}
function tankHeight(){return +$('inShape').value?mmIn('inHgtC'):mmIn('inHgt');}
function capEstimate(){const d=mmIn('inDepth');if(!d)return 0;
  return +$('inShape').value?Math.PI*Math.pow(mmIn('inDia')/2,2)*d/1e6*0.95:mmIn('inLen')*mmIn('inWid')*d/1e6*0.85;}
function profileUI(){
  const shape=+$('inShape').value,loc=+$('inLoc').value;
  $('dimRect').hidden=shape!==0;$('dimCyl').hidden=shape!==1;
  $('inPreset').disabled=shape!==0;
  const est=capEstimate();
  $('capHint').textContent=est?`Estimated from the size: about ${Math.round(est)} L. Enter the rated capacity if you know it.`:'Rated capacity from the tank label or catalogue.';
  const tips={1:`Loft tanks are shallow. The sensor cannot measure closer than ${fmtL(20,0)}–${fmtL(25,0)}, so mount it on a stand pipe (at least ${fmtL(25,0)} tall and ${fmtL(7.5,ul()==='in'?1:undefined)} wide) over the manhole, not flat on the lid.`,
    2:'Underground sump: keep the probe away from the inlet pipe and walls. The low water alarm helps protect the pump from running dry.',
    0:`Overhead tank: mount the probe at the centre of the lid or manhole, pointing straight down, at least ${fmtL(25,0)} above the full water line.`};
  setAlert($('profTip'),tips[loc]?'info':'',tips[loc]||'');
  const r=recommended();
  $('recHelp').textContent=`Recommended for ${USAGE[usageSel].toLowerCase()} use, ${LOCS[loc].toLowerCase()}: night leak check ${hh(r.nightStart)}–${hh(r.nightEnd)}, `+
    `low water alarm ${r.lowAlarm}%, leak limit ${fmtL(r.leakCm)}.`;
  $('depthShow').textContent=mmIn('inDepth')?fmtMmL(mmIn('inDepth')):'Set it in Usage & tank';
  calPreview();
}
function recommended(){const loc=+$('inLoc').value,depth=mmIn('inDepth')||spanMm();
  return {nightStart:usageSel?22:1,nightEnd:usageSel?6:5,lowAlarm:loc===2?30:usageSel?25:15,
    leakCm:Math.max(1,Math.round(depth*0.02/5)*0.5)};}
function fillProfile(){if(profLoaded||!st.profile)return;profLoaded=true;const p=st.profile;
  usageSel=p.usage;[...$('segUsage').children].forEach(b=>b.classList.toggle('on',+b.dataset.v===usageSel));
  $('inLoc').value=p.location;$('inShape').value=p.shape;buildPresets();$('inPreset').value=String(p.preset);
  if(!$('inPreset').value)$('inPreset').value='0';
  setMm('inLen',p.len);setMm('inWid',p.wid);setMm('inHgt',p.hgt);setMm('inDia',p.dia);setMm('inHgtC',p.hgt);
  setMm('inDepth',p.depth);$('inCapP').value=st.capacity||'';
  setCm('inGap',st.full);$('inNow').value=Math.round(st.valid?st.level:50);$('nowVal').textContent=$('inNow').value+'%';
  profileUI();}
[...$('segUsage').children].forEach(b=>b.onclick=()=>{usageSel=+b.dataset.v;
  [...$('segUsage').children].forEach(x=>x.classList.toggle('on',x===b));profileUI();});
$('inShape').onchange=()=>{buildPresets();profileUI();};
$('inLoc').onchange=()=>{if(+$('inLoc').value===1&&+$('inShape').value!==0){$('inShape').value='0';buildPresets();}profileUI();};
$('inPreset').onchange=()=>{const p=PRESETS[+$('inPreset').value];
  if(p){setMm('inLen',p.l);setMm('inWid',p.w);setMm('inHgt',p.h);$('inCapP').value=p.cap;setMm('inDepth',p.h-40);}profileUI();};
['inLen','inWid','inHgt','inDia','inHgtC','inDepth'].forEach(id=>$(id).addEventListener('input',()=>{
  if(['inLen','inWid','inHgt'].includes(id))$('inPreset').value='0';profileUI();}));
async function saveProfile(){
  const shape=+$('inShape').value,h=tankHeight(),d=mmIn('inDepth');
  if(d&&h&&d>h){toast('Water depth cannot be more than the tank height',true);return;}
  const cap=Math.round(iv('inCapP')||capEstimate());
  const j=await post('/api/profile',{usage:usageSel,location:$('inLoc').value,shape,preset:shape?0:$('inPreset').value,
    len:mmIn('inLen'),wid:mmIn('inWid'),hgt:h,dia:mmIn('inDia'),depth:d});
  if(!j.ok)return;
  if(cap!==st.capacity)await post('/api/settings',{capacity:cap});
  $('inCapP').value=cap||'';profLoaded=false;formLoaded=false;await poll();
  if(d&&Math.abs(d-spanMm())>15)toast('Tank saved. Calibrate below so the level matches the new water depth.');
}
async function applyRecommended(){const r=recommended();
  if(!await ask(`Apply recommended settings for ${USAGE[usageSel].toLowerCase()} use? Night leak check ${hh(r.nightStart)}–${hh(r.nightEnd)}, `+
    `low water alarm ${r.lowAlarm}%, leak limit ${r.leakCm} cm.`))return;
  const j=await post('/api/settings',{nightStart:r.nightStart,nightEnd:r.nightEnd,lowAlarm:r.lowAlarm,leakCm:r.leakCm});
  if(j.ok){await post('/api/profile',{usage:usageSel,location:$('inLoc').value});formLoaded=false;profLoaded=false;poll();}}

// ---- Calibration from the slider or from measurements ----
// E = sensor->water when empty, F = sensor->water when full (cm); depth D = E - F
function calCheck(E,F){
  if(F<15)return ['bad',`The full water line would be only ${fmtL(F)} below the sensor. It can't measure closer than about ${fmtL(20,0)}: raise the sensor on a stand pipe.`];
  if(F<22)return ['warn',`The full water line is ${fmtL(F)} below the sensor, at the edge of its blind zone. Readings near full may jump. ${fmtL(25,0)} or more is safer.`];
  if(E>450)return ['bad',`The empty point would be more than ${fmtL(450,0)} away, beyond the sensor range.`];
  return ['',''];}
function calText(E,F){const D=E-F,l=st.capacity>0?st.capacity/(D*10):0;
  return `Empty at <b>${fmtL(E)}</b> · full at <b>${fmtL(F)}</b> from the sensor · water depth ${fmtMmL(D*10)}`+
    (l?` · 1 ${ul()} ≈ ${(l*10/UN().f).toFixed(ul()==='mm'?2:1)} L`:'');}
function calPreview(){
  const D=mmIn('inDepth')/10,p=+$('inNow').value/100,box=$('prevSlider'),box2=$('prevMeas');
  $('nowVal').textContent=$('inNow').value+'%'+(st&&st.capacity?` · ${Math.round(st.capacity*p)} L`:'');
  if(!D){box.className='calprev warn';box.textContent='Enter the water depth when full in Usage & tank first.';$('btnSlider').disabled=true;}
  else if(!st||!st.valid){box.className='calprev warn';box.textContent='Waiting for a valid sensor reading.';$('btnSlider').disabled=true;}
  else{const E=st.distance+p*D,F=E-D,[c,m]=calCheck(E,F);box.className='calprev '+c;box.innerHTML=calText(E,F)+(m?'<br>'+m:'');$('btnSlider').disabled=c==='bad';}
  const G=cmIn('inGap');
  if(!D||!G){box2.className='calprev';box2.textContent='Measure from the sensor face down to the overflow (full) line.';$('btnMeas').disabled=true;}
  else{const E=G+D,[c,m]=calCheck(E,G);box2.className='calprev '+c;box2.innerHTML=calText(E,G)+(m?'<br>'+m:'');$('btnMeas').disabled=c==='bad';}
}
$('inNow').oninput=calPreview;$('inGap').oninput=calPreview;
async function saveCal(E,F,how){
  if(!await ask(`Save calibration ${how}? Empty at ${fmtL(E)}, full at ${fmtL(F)} from the sensor.`))return;
  const j=await post('/api/calibrate',{empty:E.toFixed(1),full:F.toFixed(1)});
  if(j.ok){await post('/api/profile',{gap:Math.round(F*10),depth:Math.round((E-F)*10)});formLoaded=false;profLoaded=false;poll();}}
function calSlider(){const D=mmIn('inDepth')/10,p=+$('inNow').value/100,E=st.distance+p*D;saveCal(E,E-D,`with the tank ${$('inNow').value}% full`);}
function calMeasured(){const D=mmIn('inDepth')/10,G=cmIn('inGap');saveCal(G+D,G,'from measurements');}

// ---- Overview: litres and tank at a glance ----
function renderGlance(){
  const s=st,p=s.profile||{},cap=s.capacity,lvl=s.valid?s.level:null,depth=(s.empty-s.full)*10;
  const L=v=>Math.round(v).toLocaleString()+' L';
  $('litres').textContent=cap&&lvl!==null?`≈ ${L(cap*lvl/100)} of ${L(cap)}`:'';
  $('gWater').textContent=lvl===null?'--':cap?L(cap*lvl/100):Math.round(lvl)+'%';
  $('gFree').textContent=lvl===null?'--':cap?L(cap*(100-lvl)/100):Math.round(100-lvl)+'%';
  $('gCap').textContent=cap?L(cap):'not set';
  $('gSite').textContent=siteLine()||'not named';
  $('gUsage').textContent=`${USAGE[p.usage||0]}, ${(LOCS[p.location||0]||'').toLowerCase()}`;
  const n=mm=>fmtMmL(mm).replace(' '+ul(),'');
  const dims=p.shape?(p.dia?`cylinder Ø ${n(p.dia)} × ${fmtMmL(p.hgt)}`:'vertical cylinder'):(p.len?`${n(p.len)} × ${n(p.wid)} × ${fmtMmL(p.hgt)}`:'rectangular');
  $('gTank').textContent=(p.preset&&PRESETS[p.preset]?`Loft ${PRESETS[p.preset].cap} L, `:'')+dims;
  $('gDepth').textContent=p.depth?fmtMmL(p.depth):'not set';
  $('gRange').textContent=`${fmtL(s.full)} → ${fmtL(s.empty)} (${fmtMmL(depth)})`;
  $('gGap').textContent=fmtL(s.full);
  $('gResL').textContent=`1 ${ul()} of water`;$('gRes').textContent=perUnitText(cap,depth);
  const warn=[];
  if(!p.depth&&Math.abs(s.empty-120)<0.05&&Math.abs(s.full-25)<0.05)warn.push('Not calibrated yet: the level uses default distances. Go to Setup → Calibration.');
  if(s.full<20)warn.push(`The full water line is ${fmtL(s.full)} from the sensor, inside its blind zone. Raise the sensor on a stand pipe.`);
  if(p.depth&&Math.abs(p.depth-depth)>15)warn.push(`Calibration (${depth.toFixed(0)} mm) doesn't match the tank's water depth (${p.depth} mm). Re-calibrate in Setup.`);
  setAlert($('gWarn'),warn.length?'warn':'',warn.join('<br>'));
}

// SHA-256 (hex) of a text, UTF-8 encoded. Used for the admin login challenge (crypto.subtle needs HTTPS).
function sha256(txt){
  const K=[0x428a2f98,0x71374491,0xb5c0fbcf,0xe9b5dba5,0x3956c25b,0x59f111f1,0x923f82a4,0xab1c5ed5,0xd807aa98,0x12835b01,0x243185be,0x550c7dc3,
    0x72be5d74,0x80deb1fe,0x9bdc06a7,0xc19bf174,0xe49b69c1,0xefbe4786,0x0fc19dc6,0x240ca1cc,0x2de92c6f,0x4a7484aa,0x5cb0a9dc,0x76f988da,
    0x983e5152,0xa831c66d,0xb00327c8,0xbf597fc7,0xc6e00bf3,0xd5a79147,0x06ca6351,0x14292967,0x27b70a85,0x2e1b2138,0x4d2c6dfc,0x53380d13,
    0x650a7354,0x766a0abb,0x81c2c92e,0x92722c85,0xa2bfe8a1,0xa81a664b,0xc24b8b70,0xc76c51a3,0xd192e819,0xd6990624,0xf40e3585,0x106aa070,
    0x19a4c116,0x1e376c08,0x2748774c,0x34b0bcb5,0x391c0cb3,0x4ed8aa4a,0x5b9cca4f,0x682e6ff3,0x748f82ee,0x78a5636f,0x84c87814,0x8cc70208,
    0x90befffa,0xa4506ceb,0xbef9a3f7,0xc67178f2];
  const b=Array.from(new TextEncoder().encode(txt)),l=b.length*8;b.push(0x80);while(b.length%64!==56)b.push(0);
  for(let i=7;i>=0;i--)b.push(i>3?0:(l>>>(i*8))&255);
  const H=[0x6a09e667,0xbb67ae85,0x3c6ef372,0xa54ff53a,0x510e527f,0x9b05688c,0x1f83d9ab,0x5be0cd19],w=new Array(64),r=(x,n)=>(x>>>n)|(x<<(32-n));
  for(let o=0;o<b.length;o+=64){
    for(let i=0;i<16;i++)w[i]=(b[o+i*4]<<24)|(b[o+i*4+1]<<16)|(b[o+i*4+2]<<8)|b[o+i*4+3];
    for(let i=16;i<64;i++){const s0=r(w[i-15],7)^r(w[i-15],18)^(w[i-15]>>>3),s1=r(w[i-2],17)^r(w[i-2],19)^(w[i-2]>>>10);w[i]=(w[i-16]+s0+w[i-7]+s1)|0;}
    let [a,c,d,e,f,g,h,k]=H;
    for(let i=0;i<64;i++){const t1=(k+(r(f,6)^r(f,11)^r(f,25))+((f&g)^(~f&h))+K[i]+w[i])|0,t2=((r(a,2)^r(a,13)^r(a,22))+((a&c)^(a&d)^(c&d)))|0;
      k=h;h=g;g=f;f=(e+t1)|0;e=d;d=c;c=a;a=(t1+t2)|0;}
    H[0]=(H[0]+a)|0;H[1]=(H[1]+c)|0;H[2]=(H[2]+d)|0;H[3]=(H[3]+e)|0;H[4]=(H[4]+f)|0;H[5]=(H[5]+g)|0;H[6]=(H[6]+h)|0;H[7]=(H[7]+k)|0;}
  return H.map(x=>(x>>>0).toString(16).padStart(8,'0')).join('');
}

// ---- Units: everything is stored in cm (distances) or mm (tank sizes) and converted for display ----
const UNITS=[{k:'cm',f:1},{k:'mm',f:10},{k:'in',f:1/2.54}];
let unitLocal=null;try{const v=localStorage.getItem('wtmsUnit');if(v!==null&&UNITS[+v])unitLocal=+v;}catch(e){}
const uIdx=()=>unitLocal!==null?unitLocal:(st&&UNITS[st.units]?st.units:0);
const UN=()=>UNITS[uIdx()],ul=()=>UN().k;
function udp(v){const k=ul();return k==='mm'?0:(k==='in'&&Math.abs(v)<10?2:1);}
function fmtL(cm,dp){const v=cm*UN().f;return v.toFixed(dp??udp(v))+' '+ul();}
const fmtMmL=(mm,dp)=>fmtL(mm/10,dp);
function fmtRate(cmMin){const v=cmMin*UN().f;return v.toFixed(ul()==='in'?2:ul()==='mm'?0:1)+' '+ul()+'/min';}
function setCm(id,cm){const v=cm*UN().f;$(id).value=cm||cm===0?+v.toFixed(ul()==='mm'?0:ul()==='in'?2:1):'';}
const setMm=(id,mm)=>{if(mm)setCm(id,mm/10);else $(id).value='';};
const cmIn=id=>iv(id)/UN().f, mmIn=id=>Math.round(iv(id)/UN().f*10);
function perUnitText(cap,depthMm){const cmPerU=1/UN().f,frac=cmPerU*10/depthMm;
  return (cap?`≈ ${(cap*frac).toFixed(ul()==='mm'?2:1)} L (`:'')+`${(frac*100).toFixed(ul()==='mm'?2:1)}%`+(cap?')':' of the tank');}
let lastUnit=-1;
function applyUnitLabels(){if(uIdx()===lastUnit)return;lastUnit=uIdx();
  document.querySelectorAll('.uL').forEach(e=>e.textContent=ul());
  ['inLen','inWid','inHgt','inDia','inHgtC','inDepth','inGap','inEmpty','inFull','inLeak','inFillCm'].forEach(id=>{const e=$(id);
    e.step='any';e.removeAttribute('min');e.removeAttribute('max');});
  $('unitSel').value=unitLocal===null?'':String(unitLocal);
  formLoaded=false;profLoaded=false;}
$('unitSel').onchange=e=>{const v=e.target.value;unitLocal=v===''?null:+v;
  try{v===''?localStorage.removeItem('wtmsUnit'):localStorage.setItem('wtmsUnit',v);}catch(x){}
  applyUnitLabels();if(st){render();if(aLoaded)renderAnalytics();}};
let unitDef=0;
[...$('segUnits').children].forEach(b=>b.onclick=()=>{unitDef=+b.dataset.v;[...$('segUnits').children].forEach(x=>x.classList.toggle('on',x===b));});

// ---- Admin / viewer ----
let token='';try{token=localStorage.getItem('wtmsAuth')||'';}catch(e){}
function setToken(t){token=t||'';try{t?localStorage.setItem('wtmsAuth',t):localStorage.removeItem('wtmsAuth');}catch(e){}}
const isAdmin=()=>!!(st&&st.auth&&st.auth.admin);
let pwForced=false;
function applyRole(){
  const a=isAdmin();document.body.classList.toggle('viewer',!a);
  $('btnAdmin').textContent=a?'Log out':'Admin';$('btnAdmin').title=a?'Log out of admin':'Admin login';
  document.querySelectorAll('#tabs [data-tab=setup],#tabs [data-tab=log]').forEach(b=>b.hidden=!a);
  document.querySelectorAll('#aSet input,#aSet select,#aSet button').forEach(e=>e.disabled=!a);
  document.querySelectorAll('.adminLink').forEach(e=>e.hidden=!a);
  if(!a&&(tab==='setup'||tab==='log'))showTab('overview');
  if(!a)$('banners').hidden=true;
  if(a&&st.auth.mustChange&&!$('pwModal').classList.contains('show'))openPwModal(true);
}
function openLogin(){$('loginErr').textContent='';$('inPw').value='';$('loginModal').classList.add('show');setTimeout(()=>$('inPw').focus(),50);}
function closeLogin(){$('loginModal').classList.remove('show');}
$('inPw').addEventListener('keydown',e=>{if(e.key==='Enter')doLogin();});
async function doLogin(){
  const pw=$('inPw').value;if(!pw)return;
  $('btnLogin').disabled=true;$('loginErr').textContent='';
  try{
    const a=await (await fetch('/api/auth',{cache:'no-store'})).json();
    const r=await fetch('/api/login',{method:'POST',headers:{'Content-Type':'application/x-www-form-urlencoded'},
      body:new URLSearchParams({proof:sha256(a.nonce+sha256(a.salt+pw))})});
    const j=await r.json();
    if(!j.ok)$('loginErr').textContent=j.message;
    else{setToken(j.token);closeLogin();toast('Logged in as admin');await poll();}
  }catch(e){$('loginErr').textContent='Could not reach the device';}
  $('btnLogin').disabled=false;
}
async function adminLogout(){await post('/api/logout');setToken('');toast('Logged out');await poll();}
function adminClick(){isAdmin()?adminLogout():openLogin();}
function openPwModal(forced){pwForced=forced;$('pwErr').textContent='';$('inPw1').value='';$('inPw2').value='';
  $('pwNote').textContent=forced?'You are using the default password. Choose your own admin password to continue.':'Enter a new admin password.';
  $('btnPwCancel').textContent=forced?'Log out':'Cancel';$('pwModal').classList.add('show');setTimeout(()=>$('inPw1').focus(),50);}
function closePwModal(){$('pwModal').classList.remove('show');if(pwForced)adminLogout();}
async function savePw(){
  const a=$('inPw1').value,b=$('inPw2').value;
  if(a.length<6){$('pwErr').textContent='Use at least 6 characters.';return;}
  if(a!==b){$('pwErr').textContent='The two passwords do not match.';return;}
  if(a==='admin'){$('pwErr').textContent='Choose a password other than "admin".';return;}
  try{const s=await (await fetch('/api/auth',{cache:'no-store'})).json();
    const j=await post('/api/password',{hash:sha256(s.salt+a)});
    if(j.ok){pwForced=false;$('pwModal').classList.remove('show');poll();}}
  catch(e){$('pwErr').textContent='Could not reach the device';}
}


// ---- Settings backup (export / import) and Settings ID ----
function settingsObj(){const s=st,p=s.profile||{};return {
  site:{org:s.site.org,building:s.site.building,tank:s.site.tank},
  profile:{usage:p.usage,location:p.location,shape:p.shape,preset:p.preset,lengthMm:p.len,widthMm:p.wid,heightMm:p.hgt,diameterMm:p.dia,waterDepthMm:p.depth},
  calibration:{emptyCm:+s.empty.toFixed(1),fullCm:+s.full.toFixed(1)},
  tank:{capacityL:s.capacity},
  alarms:{lowAlarmPct:s.lowAlarm},
  analytics:{nightStart:s.nightStart,nightEnd:s.nightEnd,leakCm:s.leakCm,fillCmPerMin:s.fillCm},
  display:{units:['cm','mm','inch'][s.units],leds:s.leds,brightness:s.brightness,reversed:s.reversed,colorByLevel:s.colorByLevel},
  sensor:{triggerUs:s.trigUs},
  power:{powerSaving:s.perfMode===0,txPower:['medium','high','low'][s.txLevel],hotspot:['automatic','always','on-demand'][s.apMode]},
  updateRate:{profile:['eco','balanced','responsive','custom'][s.rate.profile],sensorSeconds:s.rate.customSensorMs/1000,dashboardSeconds:s.rate.customRefreshS}};}
// Short fingerprint of the settings (not of the export time), shown in reports and exported files
function settingsId(){return sha256(JSON.stringify(settingsObj())).slice(0,8).toUpperCase();}
function exportSettings(){
  const n=new Date(),o={format:'wtms-settings',version:1,settingsId:settingsId(),exported:n.toISOString(),
    firmware:st.fw,board:st.board,device:st.wifi.host,note:'Wi-Fi and admin passwords are not included.',
    homeWifi:st.wifi.saved||'',...settingsObj()};
  const a=document.createElement('a');a.href=URL.createObjectURL(new Blob([JSON.stringify(o,null,2)+'\n'],{type:'application/json'}));
  a.download=`wtms-settings-${fileTag()}${n.getFullYear()}${pad(n.getMonth()+1)}${pad(n.getDate())}.json`;
  document.body.appendChild(a);a.click();setTimeout(()=>{URL.revokeObjectURL(a.href);a.remove();},1000);
  toast(`Settings exported (ID ${o.settingsId})`);}
async function importSettings(input){
  const f=input.files[0];input.value='';if(!f)return;
  let o;try{o=JSON.parse(await f.text());}catch(e){toast('Not a valid settings file',true);return;}
  if(o.format!=='wtms-settings'){toast('Not a Water Tanks Monitor System settings file',true);return;}
  const site=[o.site&&o.site.org,o.site&&o.site.building,o.site&&o.site.tank].filter(Boolean).join(' / ')||'no site names';
  if(!await ask(`Import settings ${o.settingsId||''} from ${f.name}? Site: ${site}. Exported ${o.exported?new Date(o.exported).toLocaleString():''} `+
    `from firmware ${o.firmware||'?'}. This replaces site, tank, calibration, alarms, analytics, display and power settings. Wi-Fi is not changed.`))return;
  const U={cm:0,mm:1,inch:2},TX={medium:0,high:1,low:2},AP={automatic:0,always:1,'on-demand':2},steps=[];
  if(o.site)steps.push(['/api/site',{org:o.site.org||'',building:o.site.building||'',tank:o.site.tank||''}]);
  if(o.profile){const q=o.profile;steps.push(['/api/profile',{usage:q.usage|0,location:q.location|0,shape:q.shape|0,preset:q.preset|0,
    len:q.lengthMm|0,wid:q.widthMm|0,hgt:q.heightMm|0,dia:q.diameterMm|0,depth:q.waterDepthMm|0}]);}
  if(o.calibration&&o.calibration.emptyCm&&o.calibration.fullCm)steps.push(['/api/calibrate',{empty:o.calibration.emptyCm,full:o.calibration.fullCm}]);
  const set={};
  if(o.tank&&o.tank.capacityL!==undefined)set.capacity=o.tank.capacityL;
  if(o.alarms)set.lowAlarm=o.alarms.lowAlarmPct;
  if(o.analytics)Object.assign(set,{nightStart:o.analytics.nightStart,nightEnd:o.analytics.nightEnd,leakCm:o.analytics.leakCm,fillCm:o.analytics.fillCmPerMin});
  if(o.display)Object.assign(set,{units:U[o.display.units]??0,leds:o.display.leds,brightness:o.display.brightness,
    reversed:o.display.reversed?1:0,colorByLevel:o.display.colorByLevel?1:0});
  if(o.sensor)set.trigUs=o.sensor.triggerUs;
  if(o.power)Object.assign(set,{perf:o.power.powerSaving?0:1,tx:TX[o.power.txPower]??0,apMode:AP[o.power.hotspot]??0});
  if(o.updateRate)Object.assign(set,{rate:{eco:0,balanced:1,responsive:2,custom:3}[o.updateRate.profile]??0,
    sensorMs:Math.round((o.updateRate.sensorSeconds||5)*1000),refreshS:o.updateRate.dashboardSeconds||10});
  Object.keys(set).forEach(k=>set[k]===undefined&&delete set[k]);
  if(Object.keys(set).length)steps.push(['/api/settings',set]);
  let ok=true;for(const [u,d] of steps){const j=await post(u,d);if(!j.ok){ok=false;break;}}
  formLoaded=false;profLoaded=false;siteLoaded=false;await poll();
  toast(ok?`Settings imported. Settings ID now ${settingsId()}`:'Import stopped: a setting was rejected',!ok);}


// ---- Update rate ----
const RATE_N=['Eco','Balanced','Responsive','Custom'],RATE_P=[[5,10],[2,5],[0.5,2]];
let rateLoaded=false;
const secTxt=v=>v<1?`${Math.round(v*1000)} ms`:`${+v.toFixed(1)} s`;
function rateVals(){const p=+$('inRate').value;return p<3?RATE_P[p]:[Math.min(30,Math.max(0.2,iv('inSensS')||5)),Math.min(60,Math.max(2,Math.round(iv('inRefS')||10)))];}
function rateUI(){const p=+$('inRate').value,[sI,rS]=rateVals(),n=sI>=2?5:7,fl=Math.min(10,Math.max(3,Math.floor(15/sI)));
  $('rateCustom').hidden=p!==3;
  $('rPerH').textContent=`${Math.round(3600/sI).toLocaleString()} per hour (every ${secTxt(sI)})`;
  $('rReact').textContent=`about ${secTxt(sI*Math.ceil(n/2))} (median of ${n})`;
  $('rFault').textContent=`about ${secTxt(sI*fl)} (${fl} missed readings)`;
  $('rRefresh').textContent=`every ${rS} s, only while the page is open`;}
function fillRate(){if(rateLoaded)return;rateLoaded=true;const r=st.rate;
  $('inRate').value=String(r.profile);$('inSensS').value=+(r.customSensorMs/1000).toFixed(1);$('inRefS').value=r.customRefreshS;rateUI();}
$('inRate').onchange=rateUI;$('inSensS').oninput=rateUI;$('inRefS').oninput=rateUI;
async function saveRate(){const p=+$('inRate').value,[sI,rS]=rateVals(),d={rate:p};
  if(p===3){d.sensorMs=Math.round(sI*1000);d.refreshS=rS;}
  const j=await post('/api/settings',d);if(j.ok){rateLoaded=false;poll();}}

// ---- Firmware update (OTA) ----
let otaBusy=false;
const kb=b=>b>=1048576?(b/1048576).toFixed(2)+' MB':Math.round(b/1024)+' KB';
function verCmp(a,b){const x=a.split('.').map(Number),y=b.split('.').map(Number);
  for(let i=0;i<3;i++){if((x[i]||0)!==(y[i]||0))return (x[i]||0)-(y[i]||0);}return 0;}
function renderOta(){$('otaCur').textContent=st.fw;$('otaBoard').textContent=st.board;$('otaMax').textContent=st.otaMax?kb(st.otaMax):'--';}
async function otaPick(input){
  const f=input.files[0];input.value='';if(!f)return;
  const buf=new Uint8Array(await f.arrayBuffer());
  if(buf[0]!==0xE9){toast('Not an ESP firmware file. Choose water_level_indicator.ino.bin.',true);return;}
  const m=new TextDecoder('latin1').decode(buf).match(/Water Tanks Monitor System (\d+\.\d+\.\d+) \| woodyouloveit\.com \| board (esp32|esp8266)/);
  if(!m){if(!await ask('This file does not look like Water Tanks Monitor System firmware. Installing other firmware removes this dashboard. Install anyway?'))return;}
  else if(m[2]!==st.boardTag){toast(`This firmware is for ${m[2]==='esp32'?'ESP32':'ESP8266 NodeMCU'}, but this device is ${st.board}.`,true);return;}
  if(st.otaMax&&f.size>st.otaMax){toast(`The file is ${kb(f.size)}, but only ${kb(st.otaMax)} is free for updates.`,true);return;}
  const nv=m?m[1]:'unknown',c=m?verCmp(nv,st.fw):1;
  if(!await ask(`Install firmware ${nv} (${kb(f.size)})? Installed now: ${st.fw}.`+(c<0?' This is an OLDER version.':c===0?' This is the same version.':'')+
    ' The device restarts afterwards and keeps all settings. Keep it powered during the update.'))return;
  otaBusy=true;$('btnOta').disabled=true;$('otaBar').hidden=false;$('otaFill').style.width='0%';$('otaMsg').textContent='Uploading…';
  const fd=new FormData();fd.append('firmware',f,f.name);
  const xhr=new XMLHttpRequest();xhr.open('POST','/api/ota?auth='+encodeURIComponent(token));
  xhr.upload.onprogress=e=>{if(e.lengthComputable){const p=Math.round(e.loaded/e.total*100);$('otaFill').style.width=p+'%';
    $('otaMsg').textContent=p<100?`Uploading ${p}% (${kb(e.loaded)} of ${kb(e.total)})`:'Verifying and installing…';}};
  xhr.onerror=()=>{otaBusy=false;$('btnOta').disabled=false;$('otaMsg').textContent='Upload failed: connection lost. The current firmware keeps running.';};
  xhr.onload=async()=>{let j={};try{j=JSON.parse(xhr.responseText);}catch(e){}
    if(!j.ok){otaBusy=false;$('btnOta').disabled=false;$('otaMsg').textContent=j.message||'Update failed.';toast(j.message||'Update failed',true);return;}
    $('otaMsg').textContent='Installed. Waiting for the device to restart…';
    for(let i=0;i<40;i++){await sleep(3000);
      try{const r=await fetch('/api/status?auth='+encodeURIComponent(token),{cache:'no-store'});const s=await r.json();
        if(s.fw===nv||(!m&&s.uptime<60)){st=s;otaBusy=false;$('btnOta').disabled=false;$('otaMsg').textContent=`Updated to ${s.fw}.`;
          toast(`Firmware updated to ${s.fw}`);if(!s.auth.admin)setToken('');render();return;}}catch(e){}}
    otaBusy=false;$('btnOta').disabled=false;$('otaMsg').textContent='The device has not come back yet. Check its power and Wi-Fi, then reload this page.';};
  xhr.send(fd);
}

// ---- Site identity ----
const siteSet=()=>st&&st.site&&(st.site.org||st.site.building||st.site.tank);
function siteLine(sep){const x=st&&st.site;if(!x)return '';return [x.org,x.building,x.tank].filter(Boolean).join(sep||' · ');}
function fileTag(){const x=st&&st.site;if(!x)return '';const t=[x.building,x.tank].filter(Boolean).join('-')
  .toLowerCase().replace(/[^a-z0-9]+/g,'-').replace(/^-|-$/g,'');return t?t+'-':'';}
function tankTitle(){const x=st.site;return [x.building,x.tank].filter(Boolean).join(' · ');}
function renderSite(){
  const x=st.site,w=st.wifi,t=tankTitle();
  $('hTitle').textContent=t||'Water Tanks Monitor System';
  $('hSub').textContent=t?(x.org?x.org+' · ':'')+'Water Tanks Monitor System':(x.org||'woodyouloveit.com');
  document.title=(t?t+' | ':'')+'Water Tanks Monitor System';
  $('fSite').textContent=siteLine()||'Water Tanks Monitor System';
  $('siteBanner').classList.toggle('show',!siteSet());
  document.querySelectorAll('.apName').forEach(e=>e.textContent=w.apName);
  const renamed=x.nextAp!==w.apName||x.nextHost!==w.host;
  $('sAp').textContent=renamed?`${w.apName} → ${x.nextAp}`:w.apName;
  $('sHost').textContent=renamed?`${w.host}.local → ${x.nextHost}.local`:`${w.host}.local`;
  setAlert($('sRestart'),renamed?'info':'',renamed?'Restart the device to use the new hotspot name and web address.':'');
  $('btnSiteRestart').style.display=renamed?'':'none';
}
async function saveSite(){
  const j=await post('/api/site',{org:$('inOrg').value,building:$('inBld').value,tank:$('inTank').value});
  if(j.ok){siteLoaded=false;await poll();}
}
let siteLoaded=false;
function fillSite(){if(siteLoaded||!st.site)return;siteLoaded=true;
  $('inOrg').value=st.site.org;$('inBld').value=st.site.building;$('inTank').value=st.site.tank;}

function fillForm(){const s=st;formLoaded=true;
  setCm('inEmpty',s.empty);setCm('inFull',s.full);unitDef=s.units;
  [...$('segUnits').children].forEach(b=>b.classList.toggle('on',+b.dataset.v===unitDef));
  $('inLeds').value=s.leds;$('inBr').value=s.brightness;$('brVal').textContent=s.brightness;
  $('inLow').value=s.lowAlarm;$('lowVal').textContent=s.lowAlarm;
  $('inRev').checked=s.reversed;$('inCbl').checked=s.colorByLevel;$('inTrig').value=s.trigUs;updateAmps();
  if(!$('inSsid').value&&s.wifi.saved)$('inSsid').value=s.wifi.saved;
  fillPower();fillAnalyticsForm();fillSite();
  $('calNowE').textContent=fmtL(s.empty);$('calNowF').textContent=fmtL(s.full);rateLoaded=false;}
// Worst case current: full tank, ~20 mA per lit color channel at full brightness, plus ~0.2 A for the board
function updateAmps(){
  const n=Math.max(1,Math.min(300,parseInt($('inLeds').value)||1)),br=$('inBr').value/255,one=$('inCbl').checked;
  let mA=0;for(let i=0;i<n;i++){const t=one?1:(n>1?i/(n-1):1);const r=t<.5?1:(1-t)*2,g=t<.5?t*2:1;mA+=(r+g)*20*br;}
  const a=mA/1000+0.2,psu=Math.max(1,Math.ceil(a*1.25));
  $('ampHelp').textContent=`Up to about ${a.toFixed(1)} A at this brightness. Use a 5V supply of at least ${psu} A.`;}
$('inLeds').oninput=updateAmps;$('inCbl').onchange=updateAmps;
$('inBr').oninput=e=>{$('brVal').textContent=e.target.value;updateAmps();};
$('inLow').oninput=e=>$('lowVal').textContent=e.target.value;

async function poll(){
  if(otaBusy)return;
  try{const live=token&&tab==='setup'?'&live=1':'';
    const r=await fetch('/api/status?auth='+encodeURIComponent(token)+live,{cache:'no-store'});st=await r.json();online=true;
    if(token&&!st.auth.admin){setToken('');toast('Admin session ended. Log in again to change settings.',true);}
    render();
    if(!st.epoch&&!timeSent){timeSent=true;fetch('/api/time',{method:'POST',headers:{'Content-Type':'application/x-www-form-urlencoded'},body:'epoch='+Math.floor(Date.now()/1000)}).catch(()=>{});}}
  catch(e){if(online)toast('Reconnecting to device…',true);online=false;
    $('chip').className='chip bad';$('chipText').textContent='Offline';}
}
async function post(url,data){
  try{const r=await fetch(url,{method:'POST',headers:{'Content-Type':'application/x-www-form-urlencoded'},
      body:new URLSearchParams(Object.assign({},data||{},token?{auth:token}:{}))});const j=await r.json();
    if(r.status===403){setToken('');toast('Admin login required',true);poll();return j;}
    toast(j.message,!j.ok);return j;}
  catch(e){toast('Request failed',true);return {ok:false};}
}

async function calNow(point){
  if(!await ask(`Save the live reading (${fmtL(st.distance)}) as ${point==='empty'?'EMPTY':'FULL'}?`))return;
  const j=await post('/api/calibrate',{point});if(j.ok){formLoaded=false;poll();}}
async function calManual(){const j=await post('/api/calibrate',{empty:cmIn('inEmpty').toFixed(1),full:cmIn('inFull').toFixed(1)});
  if(j.ok){formLoaded=false;poll();}}
async function saveSettings(){
  const n=parseInt($('inLeds').value);
  if(!(n>=1&&n<=300)){toast('Number of LEDs must be 1–300',true);return;}
  const j=await post('/api/settings',{leds:n,brightness:$('inBr').value,lowAlarm:$('inLow').value,
    reversed:$('inRev').checked?1:0,colorByLevel:$('inCbl').checked?1:0,trigUs:$('inTrig').value,units:unitDef});
  if(j.ok){formLoaded=false;poll();}}
async function resetDefaults(){if(!await ask('Reset calibration and display settings to defaults? The number of LEDs and Wi-Fi are not changed.'))return;
  const j=await post('/api/settings',{defaults:1});if(j.ok){formLoaded=false;poll();}}
async function restartDev(){if(await ask('Restart the device?'))await post('/api/restart');}

// ---- Wi-Fi ----
async function scan(){
  const b=$('btnScan');b.disabled=true;b.textContent='Scanning…';
  $('netList').innerHTML='<p class="help">Scanning for networks…</p>';
  try{
    await fetch('/api/scan?start=1',{cache:'no-store'});
    for(let i=0;i<20;i++){await sleep(1000);
      const j=await (await fetch('/api/scan',{cache:'no-store'})).json();
      if(!j.running){renderNets(j.networks||[]);break;}}
  }catch(e){$('netList').innerHTML='<p class="help">Scan failed. Try again.</p>';}
  b.disabled=false;b.textContent='Scan';
}
function renderNets(list){
  const box=$('netList');box.innerHTML='';
  if(!list.length){box.innerHTML='<p class="help">No networks found. Try again, or type the name below.</p>';return;}
  list.forEach(n=>{const b=document.createElement('button');b.type='button';b.className='net';
    const name=document.createElement('span');name.textContent=n.ssid;
    const info=document.createElement('small');info.textContent=(n.open?'Open':'🔒')+'  '+'▂▄▆█'.slice(0,bars(n.rssi));
    b.append(name,info);
    b.onclick=()=>{[...box.children].forEach(c=>c.classList.remove('sel'));b.classList.add('sel');
      $('inSsid').value=n.ssid;$('inPass').value='';if(!n.open)$('inPass').focus();};
    box.appendChild(b);});
}
function togglePw(){const p=$('inPass'),show=p.type==='password';p.type=show?'text':'password';$('btnEye').textContent=show?'Hide':'Show';}
async function connectWifi(){
  const ssid=$('inSsid').value.trim(),pass=$('inPass').value;
  if(!ssid){toast('Choose or type a network name',true);return;}
  if(pass&&(pass.length<8||pass.length>63)){toast('Password must be 8–63 characters',true);return;}
  const j=await post('/api/wifi/connect',{ssid,pass});if(j.ok)$('inPass').value='';
}
async function forgetWifi(){
  if(!await ask('Forget the saved home Wi-Fi? The device keeps working and the hotspot stays on.'))return;
  await post('/api/wifi/forget');$('inSsid').value='';
}

// ---- Power & radio ----
const AP_MODES=['Automatic','Always on','On demand (BOOT button)'],TX_LBL=['Medium, 13 dBm','High, 19.5 dBm','Low, 8.5 dBm'];
let txSel=0;
function fillPower(){const s=st;$('inEco').checked=s.perfMode===0;$('inApMode').value=String(s.apMode);txSel=s.txLevel;
  [...$('segTx').children].forEach(b=>b.classList.toggle('on',+b.dataset.v===txSel));powerUI();}
function powerUI(){const m=+$('inApMode').value,eco=$('inEco').checked;
  $('apModeHelp').textContent=[
    'On while the device has no home Wi-Fi or cannot reach it. Off 30 s after home Wi-Fi connects.',
    'Always on. Uses the most power and keeps the board warmest.',
    'Off unless needed: press the BOOT button on the board to turn it on. It turns off after 10 minutes without devices. '+
    'With no home Wi-Fi saved it is still on at start-up for setup.'][m];
}
function renderPower(){const s=st;
  $('pCpu').textContent=s.cpuMhz+' MHz';$('pTx').textContent=TX_LBL[s.txLevel];
  $('pMode').textContent=s.perfMode?'Performance':'Power saving';
  $('pRate').textContent=`${RATE_N[s.rate.profile]}, sensor every ${secTxt(s.rate.sensorMs/1000)}`;
  $('wApMode').textContent=AP_MODES[s.apMode]+(s.wifi.ap?', on now':', off now');}
[...$('segTx').children].forEach(b=>b.onclick=()=>{txSel=+b.dataset.v;[...$('segTx').children].forEach(x=>x.classList.toggle('on',x===b));});
$('inApMode').onchange=powerUI;$('inEco').onchange=powerUI;
async function savePower(){
  const m=+$('inApMode').value;
  if(m===2&&!st.wifi.saved&&!await ask('No home Wi-Fi is saved. In on-demand mode the hotspot turns off after 10 minutes without devices, '+
    'and the dashboard is then only reachable after pressing the BOOT button. Continue?'))return;
  const j=await post('/api/settings',{perf:$('inEco').checked?0:1,apMode:m,tx:txSel});
  if(j.ok){formLoaded=false;poll();}}

// ---- Connectivity log ----
const pad=n=>String(n).padStart(2,'0');
function upStr(s){return Math.floor(s/3600)+':'+pad(Math.floor(s%3600/60))+':'+pad(s%60);}
function entryTime(e){
  let ep=e.epoch;
  if(!ep&&st&&st.epoch&&e.boot===st.boot)ep=st.epoch-(st.uptime-e.up);
  return ep?new Date(ep*1000):null;}
function fmtTime(e){const d=entryTime(e);
  return d?d.toLocaleString([], {day:'2-digit',month:'short',hour:'2-digit',minute:'2-digit',second:'2-digit',hour12:false})
          :`Boot #${e.boot} +${upStr(e.up)}`;}
function parseLog(txt){return txt.split('\n').map(l=>l.split('\t')).filter(f=>f.length>=6)
  .map(f=>({boot:+f[0],up:+f[1],epoch:+f[2],lvl:f[3],cat:f[4],msg:f.slice(5).join(' ')}));}
async function loadLog(){
  try{if(!isAdmin())return;const r=await fetch('/api/log?auth='+encodeURIComponent(token),{cache:'no-store'});if(!r.ok)return;logRows=parseLog(await r.text());renderLog();}
  catch(e){$('logBox').innerHTML='<p class="help">Could not load the log.</p>';}}
function renderLog(){
  const f=$('logFilter').value,box=$('logBox');
  const count=(fn)=>logRows.filter(fn).length;
  const stats=[
    ['Restarts',count(e=>e.cat==='boot'&&e.msg.startsWith('Boot #')),''],
    ['Crashes / power dips',count(e=>e.cat==='boot'&&(e.lvl==='E'||e.msg.includes('Power on'))),'bad'],
    ['Hotspot turned off',count(e=>e.msg.startsWith('Hotspot off')),''],
    ['Hotspot channel changes',count(e=>e.msg.startsWith('Hotspot channel')),'warn'],
    ['Home Wi-Fi drops',count(e=>e.msg.startsWith('Home Wi-Fi lost')),'warn'],
    ['Warnings',count(e=>e.lvl==='W'),'warn']];
  $('logStats').innerHTML=stats.map(([k,v,c])=>`<div class="stat ${v?c:''}"><b>${v}</b>${k}</div>`).join('');
  const rows=logRows.filter(e=>f==='all'||(f==='net'&&(e.cat==='wifi'||e.cat==='ap'))||
    (f==='warn'&&e.lvl!=='I')||(f==='boot'&&e.cat==='boot')).slice().reverse();
  box.innerHTML='';
  if(!rows.length){box.innerHTML='<p class="help">No events yet.</p>';return;}
  const frag=document.createDocumentFragment();
  rows.forEach(e=>{const r=document.createElement('div');r.className='lr '+e.lvl+(e.cat==='boot'?' boot':'');
    const t=document.createElement('time');t.textContent=fmtTime(e);
    const g=document.createElement('span');g.className='tag';g.textContent=e.cat;
    const m=document.createElement('span');m.className='msg';m.textContent=e.msg;
    r.append(t,g,m);frag.appendChild(r);});
  box.appendChild(frag);}
function downloadLog(){
  const lines=logRows.map(e=>{const d=entryTime(e);
    const t=d?`${d.getFullYear()}-${pad(d.getMonth()+1)}-${pad(d.getDate())} ${pad(d.getHours())}:${pad(d.getMinutes())}:${pad(d.getSeconds())}`
             :`boot#${e.boot} +${upStr(e.up)}`;
    return `${t}\t${e.lvl}\t${e.cat}\t${e.msg}`;});
  const head=(st?`Water Tanks Monitor System log · ${siteLine()||'site not named'}\nfirmware ${st.fw} · ${st.board} · ${st.wifi.host}.local · downloaded ${new Date().toString()}\n`:'')+
    `woodyouloveit.com · © 2026 Chanchal Sakarde. All Rights Reserved.\n\n`;
  const a=document.createElement('a');a.href=URL.createObjectURL(new Blob([head+lines.join('\n')+'\n'],{type:'text/plain'}));
  const n=new Date();a.download=`wtms-log-${fileTag()}${n.getFullYear()}${pad(n.getMonth()+1)}${pad(n.getDate())}-${pad(n.getHours())}${pad(n.getMinutes())}.txt`;
  document.body.appendChild(a);a.click();setTimeout(()=>{URL.revokeObjectURL(a.href);a.remove();},500);}
async function clearLog(){if(!await ask('Clear the connectivity log? This cannot be undone.'))return;
  await post('/api/log/clear');loadLog();}

// ================= Tabs =================
let tab='overview';
const TABS={overview:'tabOverview',analytics:'tabAnalytics',setup:'tabSetup',log:'tabLog'};
function showTab(t){
  // "#cWifi" etc. open the tab that holds that card and scroll to it
  let target=null;
  if(!TABS[t]){const el=t&&document.getElementById(t),m=el&&el.closest('main.tab');
    if(m){target=el;t=Object.keys(TABS).find(k=>TABS[k]===m.id);}}
  const prevTab=tab;
  tab=TABS[t]?t:'overview';
  if(st&&tab!==prevTab)setTimeout(poll,0);   // refresh at once (e.g. live readings on Setup)
  document.querySelectorAll('.tabs button').forEach(b=>b.classList.toggle('on',b.dataset.tab===tab));
  for(const k in TABS)$(TABS[k]).hidden=tab!==k;
  if(target)setTimeout(()=>target.scrollIntoView({behavior:'smooth',block:'start'}),50);
  if(tab==='analytics')loadAnalytics();if(tab==='log')loadLog();}
document.querySelectorAll('.tabs button').forEach(b=>b.onclick=()=>{location.hash=b.dataset.tab;});
window.addEventListener('hashchange',()=>showTab(location.hash.slice(1)));

// ================= Analytics =================
let hist=[],fills=[],aLoaded=false,rangeH=24,ana=null;
const DAY=86400,hh=h=>pad(h)+':00';
const nowT=()=>st&&st.epoch?st.epoch:Math.floor(Date.now()/1000);
const spanMm=()=>(st.empty-st.full)*10;
const pctOf=mm=>Math.min(100,Math.max(0,(st.empty*10-mm)/spanMm()*100));
const lpm=()=>st.capacity>0?st.capacity/spanMm():0;
function amt(mm,signed){const s=signed&&mm>0?'+':'';const l=lpm();
  return l?s+Math.round(mm*l).toLocaleString()+' L':s+(mm/spanMm()*100).toFixed(1)+'%';}
function dur(min){min=Math.round(min);return min<60?min+' min':Math.floor(min/60)+' h '+pad(min%60)+' min';}
const dayKey=t=>{const d=new Date(t*1000);return d.getFullYear()+'-'+pad(d.getMonth()+1)+'-'+pad(d.getDate());};
const dayLbl=(t,long)=>new Date(t*1000).toLocaleDateString([], long?{weekday:'short',day:'2-digit',month:'short'}:{weekday:'short'});
const tLbl=t=>new Date(t*1000).toLocaleString([], {weekday:'short',hour:'2-digit',minute:'2-digit',hour12:false});
function startOfDay(t){const d=new Date(t*1000);d.setHours(0,0,0,0);return d.getTime()/1000;}
function median(a){if(!a.length)return null;const s=a.slice().sort((x,y)=>x-y);return s[s.length>>1];}

async function loadAnalytics(){
  try{
    const [hb,fb]=await Promise.all([fetch('/api/history',{cache:'no-store'}).then(r=>r.arrayBuffer()),
                                     fetch('/api/fills',{cache:'no-store'}).then(r=>r.arrayBuffer())]);
    const dv=new DataView(hb);hist=[];
    for(let o=0;o+8<=hb.byteLength;o+=8){const mm=dv.getUint16(o+4,true);
      hist.push({t:dv.getUint32(o,true),mm:mm===65535?null:mm,fill:dv.getUint16(o+6,true)&1});}
    hist.sort((a,b)=>a.t-b.t);
    const fv=new DataView(fb);fills=[];
    for(let o=0;o+12<=fb.byteLength;o+=12)fills.push({s:fv.getUint32(o,true),e:fv.getUint32(o+4,true),smm:fv.getUint16(o+8,true),emm:fv.getUint16(o+10,true)});
    fills.sort((a,b)=>a.s-b.s);aLoaded=true;
  }catch(e){aLoaded=false;}
  if(st)renderAnalytics();
}

// Water used: follow the level with a small dead band so sensor noise is not counted
function usageEvents(){
  const DB=3,out=[];let ref=null,prevT=0;
  for(const r of hist){
    if(r.mm===null){continue;}
    if(r.fill||ref===null||r.t-prevT>900){ref=r.mm;prevT=r.t;continue;}
    prevT=r.t;
    if(r.mm>ref+DB){out.push({t:r.t,mm:r.mm-DB-ref});ref=r.mm-DB;}
    else if(r.mm<ref-DB)ref=r.mm+DB;
  }
  return out;
}
function allFills(){const f=fills.map(x=>({...x,live:false}));
  if(st.filling&&st.fillStart)f.push({s:st.fillStart,e:nowT(),smm:null,emm:null,live:true});return f;}

function nightChecks(){
  const res=[],now=nowT(),hours=((st.nightEnd-st.nightStart+24)%24)||24,leak=st.leakCm*10;
  for(let k=0;k<7;k++){
    const d=new Date(now*1000);d.setDate(d.getDate()-k);d.setHours(st.nightEnd,0,0,0);
    const end=d.getTime()/1000,start=end-hours*3600;if(end>now)continue;
    const rec=hist.filter(r=>r.t>=start&&r.t<=end),valid=rec.filter(r=>r.mm!==null);
    const row={end,start,hours,drop:null,status:'na',text:'No data'};
    if(valid.length<hours*30*0.6){res.push(row);continue;}
    if(rec.some(r=>r.fill)||fills.some(f=>f.s<end&&f.e>start)){row.text='Tank was filling';res.push(row);continue;}
    const a=median(valid.slice(0,5).map(r=>r.mm)),b=median(valid.slice(-5).map(r=>r.mm));
    row.drop=b-a;
    // A leak drops slowly and steadily; someone using water drops it in one step.
    // Each hour is measured from the end of the previous one, so a drop right on the hour is not missed.
    let maxHour=0,prev=median(valid.slice(0,3).map(r=>r.mm));
    for(let h=0;h<hours;h++){const s=valid.filter(r=>r.t>=start+h*3600&&r.t<start+(h+1)*3600);
      if(s.length<3)continue;const endH=median(s.slice(-3).map(r=>r.mm));maxHour=Math.max(maxHour,endH-prev);prev=endH;}
    if(row.drop>=leak&&hours>=3&&maxHour>=0.7*row.drop){row.status='warn';row.text='Water used (one drop)';}
    else if(row.drop>=leak){row.status='bad';row.text='Possible leak';}
    else if(row.drop>=leak/2){row.status='warn';row.text='Watch';}
    else{row.status='ok';row.text='OK';}
    res.push(row);
  }
  return res;
}

// ---------- charts (plain SVG, no libraries) ----------
const NS='http://www.w3.org/2000/svg';
function el(tag,attrs,parent){const e=document.createElementNS(NS,tag);for(const k in attrs)e.setAttribute(k,attrs[k]);if(parent)parent.appendChild(e);return e;}
function css(v){return getComputedStyle(document.documentElement).getPropertyValue(v).trim();}

function levelChart(box){
  box.innerHTML='';const W=Math.max(300,box.clientWidth),H=Math.round(Math.min(280,Math.max(190,W*0.32)));
  const L=36,Rr=10,T=10,B=26,end=nowT(),start=end-rangeH*3600;
  const x=t=>L+(t-start)/(end-start)*(W-L-Rr),y=p=>T+(100-p)/100*(H-T-B);
  const svg=el('svg',{viewBox:`0 0 ${W} ${H}`},box);
  // night bands
  for(let d=startOfDay(start)-DAY;d<=end;d+=DAY){
    let s=d+st.nightStart*3600,e=d+st.nightEnd*3600;if(e<=s)e+=DAY;
    const a=Math.max(s,start),b=Math.min(e,end);if(b>a)el('rect',{x:x(a),y:T,width:x(b)-x(a),height:H-T-B,fill:'rgba(100,116,139,.16)'},svg);}
  // fill bands
  for(const f of allFills()){const a=Math.max(f.s,start),b=Math.min(f.e,end);
    if(b>a)el('rect',{x:x(a),y:T,width:Math.max(2,x(b)-x(a)),height:H-T-B,fill:'rgba(22,163,74,.22)'},svg);}
  // grid
  for(const p of [0,25,50,75,100]){el('line',{x1:L,x2:W-Rr,y1:y(p),y2:y(p),class:'grid'},svg);
    el('text',{x:L-6,y:y(p)+4,'text-anchor':'end',class:'axis'},svg).textContent=p+'%';}
  // x ticks
  const step=rangeH<=24?(W<500?6:3)*3600:DAY;
  let t0=rangeH<=24?Math.ceil(start/step)*step:startOfDay(start)+DAY;
  if(rangeH<=24){const d=new Date(start*1000);d.setMinutes(0,0,0);t0=d.getTime()/1000;while(t0<start||new Date(t0*1000).getHours()%(step/3600))t0+=3600;}
  for(let t=t0;t<=end;t+=step){el('line',{x1:x(t),x2:x(t),y1:T,y2:H-B,class:'grid','stroke-dasharray':'2 3'},svg);
    el('text',{x:x(t),y:H-8,'text-anchor':'middle',class:'axis'},svg).textContent=rangeH<=24?hh(new Date(t*1000).getHours()):dayLbl(t);}
  // line + area, broken at gaps
  const pts=hist.filter(r=>r.t>=start-300&&r.t<=end);let seg=[],segs=[];
  for(const r of pts){if(r.mm===null||(seg.length&&r.t-seg[seg.length-1].t>600)){if(seg.length)segs.push(seg);seg=[];}if(r.mm!==null)seg.push(r);}
  if(seg.length)segs.push(seg);
  const acc=css('--accent');
  for(const s of segs){const d=s.map((r,i)=>(i?'L':'M')+x(r.t).toFixed(1)+','+y(pctOf(r.mm)).toFixed(1)).join('');
    el('path',{d:d+`L${x(s[s.length-1].t).toFixed(1)},${y(0)}L${x(s[0].t).toFixed(1)},${y(0)}Z`,fill:acc,opacity:.12},svg);
    el('path',{d,fill:'none',stroke:acc,'stroke-width':2,'stroke-linejoin':'round'},svg);}
  if(!pts.length){el('text',{x:W/2,y:H/2,'text-anchor':'middle',class:'axis'},svg).textContent='No history in this range yet';}
  // hover / touch tooltip
  const tip=document.createElement('div');tip.className='tip';box.appendChild(tip);
  const cur=el('line',{y1:T,y2:H-B,stroke:css('--muted'),'stroke-width':1,visibility:'hidden'},svg);
  const move=ev=>{const rc=svg.getBoundingClientRect(),px=(ev.clientX-rc.left)*W/rc.width,t=start+(px-L)/(W-L-Rr)*(end-start);
    let best=null;for(const r of pts)if(r.mm!==null&&(!best||Math.abs(r.t-t)<Math.abs(best.t-t)))best=r;
    if(!best||Math.abs(best.t-t)>1800){tip.style.display='none';cur.setAttribute('visibility','hidden');return;}
    const X=x(best.t);cur.setAttribute('x1',X);cur.setAttribute('x2',X);cur.setAttribute('visibility','visible');
    tip.textContent=`${tLbl(best.t)} · ${pctOf(best.mm).toFixed(0)}%${best.fill?' · filling':''}`;
    tip.style.left=(X/W*100)+'%';tip.style.display='block';};
  svg.addEventListener('pointermove',move);svg.addEventListener('pointerdown',move);
  svg.addEventListener('pointerleave',()=>{tip.style.display='none';cur.setAttribute('visibility','hidden');});
}

function barChart(box,labels,values,fmt,hl,short){
  box.innerHTML='';const W=Math.max(280,box.clientWidth),H=190,L=8,Rr=8,T=18,B=24;
  const svg=el('svg',{viewBox:`0 0 ${W} ${H}`},box),max=Math.max(...values,0);
  if(!max){el('text',{x:W/2,y:H/2,'text-anchor':'middle',class:'axis'},svg).textContent='Not enough data yet';return;}
  const n=values.length,bw=(W-L-Rr)/n,acc=css('--accent'),dim=css('--line'),f=short&&bw<60?short:fmt;
  el('line',{x1:L,x2:W-Rr,y1:H-B,y2:H-B,class:'grid'},svg);
  values.forEach((v,i)=>{const h=v/max*(H-T-B),X=L+i*bw+bw*0.15,w=bw*0.7;
    el('rect',{x:X,y:H-B-h,width:w,height:Math.max(v?1:0,h),rx:3,fill:hl&&!hl.has(i)?dim:acc},svg);
    if(n<=10&&v)el('text',{x:X+w/2,y:H-B-h-5,'text-anchor':'middle',class:'axis'},svg).textContent=f(v);
    if(n<=10||i%3===0)el('text',{x:X+w/2,y:H-7,'text-anchor':'middle',class:'axis'},svg).textContent=labels[i];});
}

function renderAnalytics(){
  const msg=$('aMsg');
  if(st.logStore!=='flash'){setAlert(msg,'bad','History needs flash storage. On ESP8266 select Tools → Flash Size → 4MB (FS:2MB) and upload again.');}
  else if(!st.epoch){setAlert(msg,'info','Waiting for the clock. History is recorded once the device knows the time: connect it to home Wi-Fi, or keep this page open (your browser sets the clock).');}
  else if(!aLoaded){setAlert(msg,'bad','Could not load history from the device.');}
  else if(hist.length<5){setAlert(msg,'info','Collecting data. A point is recorded every 2 minutes; fill, usage and night statistics appear after a few hours.');}
  else setAlert(msg,'','');
  if(!aLoaded)return;
  const now=nowT(),today=startOfDay(now),use=usageEvents(),af=allFills(),nights=nightChecks();
  // ---- daily buckets, last 7 days ----
  const days=[];for(let k=6;k>=0;k--)days.push(today-k*DAY);
  const motor=days.map(d=>af.filter(f=>f.s>=d&&f.s<d+DAY).reduce((a,f)=>a+(f.e-f.s)/60,0));
  const used=days.map(d=>use.filter(u=>u.t>=d&&u.t<d+DAY).reduce((a,u)=>a+u.mm,0));
  const dl=days.map(d=>dayLbl(d));
  barChart($('motorChart'),dl,motor,v=>dur(v),null,v=>Math.round(v)+'m');
  const l=lpm(),kL=v=>{const x=v*l;return x>=1000?(x/1000).toFixed(1)+'kL':Math.round(x)+'L';};
  barChart($('useChart'),dl,used,v=>l?Math.round(v*l)+'L':(v/spanMm()*100).toFixed(0)+'%',null,v=>l?kL(v):(v/spanMm()*100).toFixed(0)+'%');
  // ---- hour of day ----
  const dayCount=new Set(hist.filter(r=>r.mm!==null).map(r=>dayKey(r.t))).size||1;
  const hours=Array(24).fill(0);use.forEach(u=>hours[new Date(u.t*1000).getHours()]+=u.mm);
  const avgH=hours.map(v=>v/dayCount),top=avgH.map((v,i)=>[v,i]).sort((a,b)=>b[0]-a[0]).filter(x=>x[0]>0).slice(0,3).map(x=>x[1]);
  barChart($('hourChart'),avgH.map((_,i)=>pad(i)),avgH,v=>amt(v),new Set(top));
  const totH=avgH.reduce((a,b)=>a+b,0);
  $('hourHelp').textContent=top.length?`Average per day over ${dayCount} day${dayCount>1?'s':''}. Busiest: `+top.map(i=>`${hh(i)}–${hh((i+1)%24)} (${Math.round(avgH[i]/totH*100)}%)`).join(', ')+'.':'Average per day. Appears once water use has been recorded.';
  // ---- fills ----
  const done=fills.filter(f=>f.e-f.s>=180);
  const rate=done.length?done.reduce((a,f)=>a+(f.smm-f.emm),0)/done.reduce((a,f)=>a+(f.e-f.s)/60,0):0;
  $('fillList').innerHTML='';
  done.slice(-5).reverse().forEach(f=>{const d=document.createElement('div');
    d.innerHTML=`<span>${new Date(f.s*1000).toLocaleString([], {weekday:'short',day:'2-digit',month:'short',hour:'2-digit',minute:'2-digit',hour12:false})}</span><span>${dur((f.e-f.s)/60)} · ${amt(f.smm-f.emm,true)}</span>`;
    $('fillList').appendChild(d);});
  if(!done.length)$('fillList').innerHTML='<div><span class="help">No fills recorded yet.</span><span></span></div>';
  // ---- night table ----
  const leakRow=nights.find(n=>n.status!=='na'&&n.text!=='Tank was filling');
  $('nightTable').innerHTML='<table class="nt"><thead><tr><th>Night</th><th>Change</th><th>Per hour</th><th>Result</th></tr></thead><tbody>'+
    nights.map(n=>`<tr><td>${dayLbl(n.end,true)}</td><td>${n.drop===null?'–':(n.drop>0?'−':'+')+amt(Math.abs(n.drop))}</td>`+
      `<td>${n.drop===null?'–':amt(Math.abs(n.drop)/n.hours)}</td><td><span class="pill ${n.status}">${n.text}</span></td></tr>`).join('')+'</tbody></table>';
  $('nightHelp').textContent=`Level change between ${hh(st.nightStart)} and ${hh(st.nightEnd)} each night. `+
    `"Possible leak" when it drops ${fmtL(st.leakCm)}${l?' ('+Math.round(st.leakCm*10*l)+' L)':''} or more, slowly and steadily, with no fill running. `+
    `"Water used (one drop)" when most of it happened within one hour, like a tap or flush. "Watch" from half of the limit.`;
  // ---- KPIs ----
  const k=[];const last=done[done.length-1];
  if(st.filling)k.push(['live','NOW','Filling',st.fillEta>=0?`full in ~${dur(st.fillEta)} · ${fmtRate(st.fillRate)}`:fmtRate(st.fillRate)]);
  else k.push(['','NOW',st.valid?Math.round(st.level)+'%':'–','motor off']);
  k.push(['','LAST FILL',last?amt(last.smm-last.emm,true):'–',last?`${tLbl(last.s)} · ${dur((last.e-last.s)/60)}`:'none recorded yet']);
  k.push(['','EMPTY → FULL TAKES',rate>0?'≈ '+dur(spanMm()/rate):'–',rate>0?`average of ${done.length} fill${done.length>1?'s':''}`:'needs one full fill']);
  k.push(['','MOTOR TODAY',dur(motor[6]),`${af.filter(f=>f.s>=today).length} fill(s) · 7-day avg ${dur(motor.reduce((a,b)=>a+b,0)/7)}`]);
  k.push(['','USED TODAY',amt(used[6]),`yesterday ${amt(used[5])}`]);
  k.push(['','BUSIEST HOUR',top.length?hh(top[0])+'–'+hh((top[0]+1)%24):'–',top.length?`${amt(avgH[top[0]])} per day`:'not enough data']);
  if(leakRow)k.push([leakRow.status,'LAST NIGHT',leakRow.text,leakRow.drop===null?'':`${leakRow.drop>0?'−':'+'}${amt(Math.abs(leakRow.drop))} between ${hh(st.nightStart)}–${hh(st.nightEnd)}`]);
  else k.push(['','LAST NIGHT','–','no complete night yet']);
  ana={now,today,days,dl,motor,used,avgH,top,dayCount,done,nights,rate,k,af,use};
  $('kpis').innerHTML=k.map(([c,a,b,s])=>`<div class="kpi ${c}"><span>${a}</span><b>${b}</b><small>${s}</small></div>`).join('');
  if(tab==='analytics')levelChart($('levelChart'));
  // overview leak banner
  const lb=$('alertLeak');
  if(leakRow&&leakRow.status==='bad'&&now-leakRow.end<DAY)setAlert(lb,'bad',`Possible leak last night: level dropped ${amt(leakRow.drop)} between ${hh(st.nightStart)} and ${hh(st.nightEnd)}. <a href="#analytics">See analytics</a>`);
  else setAlert(lb,'','');
}
document.querySelectorAll('#rangeSeg button').forEach(b=>b.onclick=()=>{rangeH=+b.dataset.h;
  document.querySelectorAll('#rangeSeg button').forEach(x=>x.classList.toggle('on',x===b));levelChart($('levelChart'));});
let rsz;window.addEventListener('resize',()=>{clearTimeout(rsz);rsz=setTimeout(()=>{if(aLoaded&&st)renderAnalytics();},200);});

for(let i=0;i<24;i++){$('inNs').add(new Option(hh(i),i));$('inNe').add(new Option(hh(i),i));}
function fillAnalyticsForm(){$('inCap').value=st.capacity;setCm('inFillCm',st.fillCm);$('inNs').value=st.nightStart;$('inNe').value=st.nightEnd;setCm('inLeak',st.leakCm);}
async function saveAnalytics(){
  if($('inNs').value===$('inNe').value){toast('Night window start and end must differ',true);return;}
  const j=await post('/api/settings',{capacity:$('inCap').value||0,fillCm:cmIn('inFillCm').toFixed(2),nightStart:$('inNs').value,nightEnd:$('inNe').value,leakCm:cmIn('inLeak').toFixed(2)});
  if(j.ok){formLoaded=false;await poll();renderAnalytics();}}
async function clearHistory(){if(!await ask('Clear all tank history and recorded fills? This cannot be undone.'))return;
  await post('/api/history/clear');loadAnalytics();}

// ================= PDF report (written directly in the browser, no libraries) =================
const BRAND={site:'woodyouloveit.com',url:'https://woodyouloveit.com',owner:'Chanchal Sakarde',year:'2026',
  repo:'github.com/ChanchalSakardeQH/WATERTANK-LEVEL-INDICATOR-with-Dashboard'};
// Helvetica / Helvetica-Bold character widths for ASCII 32..126 (standard AFM metrics)
const HW=[278,278,355,556,556,889,667,191,333,333,389,584,278,333,278,278,556,556,556,556,556,556,556,556,556,556,278,278,584,584,584,556,1015,667,667,722,722,667,611,778,722,278,500,667,556,833,722,778,667,778,722,667,611,722,667,944,667,667,611,278,278,278,469,556,333,556,556,500,556,556,278,556,556,222,222,500,222,833,556,556,556,556,333,500,278,556,500,722,500,500,500,334,260,334,584];
const HBW=[278,333,474,556,556,889,722,238,333,333,389,584,278,333,278,278,556,556,556,556,556,556,556,556,556,556,333,333,584,584,584,611,975,722,722,722,722,667,611,778,722,278,556,722,611,833,722,778,667,778,722,667,611,722,667,944,667,667,611,333,278,333,584,556,333,556,611,556,611,556,333,611,611,278,278,556,278,889,611,611,611,611,389,556,333,611,556,778,556,556,500,389,280,389,584];
const HX={0x96:556,0x97:1000,0xa9:737,0xb7:278,0xb0:400,0xd7:584,0x95:350,0x85:1000};
const WA={'\u2013':'\x96','\u2014':'\x97','\u00b7':'\xb7','\u00a9':'\xa9','\u00b0':'\xb0','\u00d7':'\xd7','\u2022':'\x95',
  '\u2026':'\x85','\u2018':"'",'\u2019':"'",'\u201c':'"','\u201d':'"','\u2248':'~','\u2192':'->','\u2212':'-','\u00a0':' '};
function wa(s){let o='';for(const ch of String(s)){const c=ch.codePointAt(0);
  if(WA[ch]!==undefined)o+=WA[ch];else if(c<256)o+=ch;else if(c<0x1f000)o+='?';}return o;}
function tw(s,size,bold){const t=bold?HBW:HW;let w=0;
  for(let i=0;i<s.length;i++){const c=s.charCodeAt(i);w+=c>=32&&c<=126?t[c-32]:(HX[c]||556);}return w*size/1000;}

class Pdf{
  constructor(){this.W=595.28;this.H=841.89;this.pages=[];this.img=null;}
  page(){this.c=[];this.pages.push(this.c);}
  o(s){this.c.push(s);}
  col(hex){const n=parseInt(hex.slice(1),16);return [(n>>16)&255,(n>>8)&255,n&255].map(v=>(v/255).toFixed(3)).join(' ');}
  Y(y){return (this.H-y).toFixed(2);}
  rect(x,y,w,h,fill,stroke,lw){
    if(fill)this.o(this.col(fill)+' rg');if(stroke)this.o(this.col(stroke)+' RG '+(lw||0.6)+' w');
    this.o(`${x.toFixed(2)} ${(this.H-y-h).toFixed(2)} ${w.toFixed(2)} ${h.toFixed(2)} re ${fill&&stroke?'B':fill?'f':'S'}`);}
  line(x1,y1,x2,y2,hex,lw,dash){
    this.o(`${this.col(hex)} RG ${lw||0.6} w ${dash?'[2 2] 0 d':''} ${x1.toFixed(2)} ${this.Y(y1)} m ${x2.toFixed(2)} ${this.Y(y2)} l S${dash?' [] 0 d':''}`);}
  poly(pts,hex,lw,fill,baseY){
    if(pts.length<2)return;
    const seg=pts.map((p,i)=>`${p[0].toFixed(2)} ${this.Y(p[1])} ${i?'l':'m'}`).join(' ');
    if(fill)this.o(`${this.col(fill)} rg ${seg} ${pts[pts.length-1][0].toFixed(2)} ${this.Y(baseY)} l ${pts[0][0].toFixed(2)} ${this.Y(baseY)} l h f`);
    this.o(`${this.col(hex)} RG ${lw} w 1 j ${seg} S`);}
  text(x,y,s,size,opt={}){
    const t=wa(s),w=tw(t,size,opt.bold);
    if(opt.align==='right')x-=w;else if(opt.align==='center')x-=w/2;
    const esc=t.replace(/\\/g,'\\\\').replace(/\(/g,'\\(').replace(/\)/g,'\\)');
    this.o(`${this.col(opt.color||'#0f172a')} rg BT /${opt.bold?'F2':'F1'} ${size} Tf ${x.toFixed(2)} ${this.Y(y)} Td (${esc}) Tj ET`);
    return w;}
  wrap(x,y,s,size,maxW,lh,opt={}){
    let line='';
    for(const wd of wa(s).split(' ')){const test=line?line+' '+wd:wd;
      if(tw(test,size,opt.bold)>maxW&&line){this.text(x,y,line,size,opt);y+=lh;line=wd;}else line=test;}
    if(line){this.text(x,y,line,size,opt);y+=lh;}
    return y;}
  image(x,y,w,h){this.o(`q ${w.toFixed(2)} 0 0 ${h.toFixed(2)} ${x.toFixed(2)} ${(this.H-y-h).toFixed(2)} cm /Im1 Do Q`);}
  blob(info){
    const enc=s=>{const a=new Uint8Array(s.length);for(let i=0;i<s.length;i++)a[i]=s.charCodeAt(i)&255;return a;};
    const pstr=s=>'('+wa(s).replace(/\\/g,'\\\\').replace(/\(/g,'\\(').replace(/\)/g,'\\)')+')';
    const parts=[],offs=[],objs=[];let len=0;
    const add=x=>{const b=typeof x==='string'?enc(x):x;parts.push(b);len+=b.length;};
    const nP=this.pages.length,first=6,infoN=first+nP*2;
    objs[1]='<< /Type /Catalog /Pages 2 0 R >>';
    objs[2]=`<< /Type /Pages /Kids [${this.pages.map((_,i)=>(first+i*2)+' 0 R').join(' ')}] /Count ${nP} >>`;
    objs[3]='<< /Type /Font /Subtype /Type1 /BaseFont /Helvetica /Encoding /WinAnsiEncoding >>';
    objs[4]='<< /Type /Font /Subtype /Type1 /BaseFont /Helvetica-Bold /Encoding /WinAnsiEncoding >>';
    objs[5]=this.img?{head:`<< /Type /XObject /Subtype /Image /Width ${this.img.w} /Height ${this.img.h} /ColorSpace /DeviceRGB `+
      `/BitsPerComponent 8 /Filter /DCTDecode /Length ${this.img.data.length} >>\nstream\n`,bin:this.img.data,tail:'\nendstream'}:'<< >>';
    const res=`<< /Font << /F1 3 0 R /F2 4 0 R >>${this.img?' /XObject << /Im1 5 0 R >>':''} >>`;
    this.pages.forEach((c,i)=>{const n=first+i*2,body=c.join('\n');
      objs[n]=`<< /Type /Page /Parent 2 0 R /MediaBox [0 0 ${this.W} ${this.H}] /Resources ${res} /Contents ${n+1} 0 R >>`;
      objs[n+1]={head:`<< /Length ${body.length} >>\nstream\n`,bin:enc(body),tail:'\nendstream'};});
    objs[infoN]=`<< /Title ${pstr(info.title)} /Author ${pstr(info.author)} /Subject ${pstr(info.subject)} /Creator ${pstr(info.creator)} /Producer ${pstr(info.creator)} >>`;
    add('%PDF-1.4\n%\xe2\xe3\xcf\xd3\n');
    for(let n=1;n<objs.length;n++){offs[n]=len;add(n+' 0 obj\n');const o=objs[n];
      if(typeof o==='string')add(o);else{add(o.head);add(o.bin);add(o.tail);}add('\nendobj\n');}
    const xref=len;let x=`xref\n0 ${objs.length}\n0000000000 65535 f \n`;
    for(let n=1;n<objs.length;n++)x+=String(offs[n]).padStart(10,'0')+' 00000 n \n';
    add(x+`trailer\n<< /Size ${objs.length} /Root 1 0 R /Info ${infoN} 0 R >>\nstartxref\n${xref}\n%%EOF\n`);
    return new Blob(parts,{type:'application/pdf'});}
}

async function logoJpeg(){
  const img=$('brandLogo');if(!img)return null;
  if(!img.complete)await new Promise(r=>{img.onload=r;img.onerror=r;});
  const s=2,c=document.createElement('canvas');c.width=img.naturalWidth*s;c.height=img.naturalHeight*s;
  const g=c.getContext('2d');g.fillStyle='#ffffff';g.fillRect(0,0,c.width,c.height);g.drawImage(img,0,0,c.width,c.height);
  const bin=atob(c.toDataURL('image/jpeg',0.92).split(',')[1]),a=new Uint8Array(bin.length);
  for(let i=0;i<bin.length;i++)a[i]=bin.charCodeAt(i);
  return {w:c.width,h:c.height,data:a};
}
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
